karlp/hubbish/parts/1912251634_Ningbo-Kangnex-Elec-WJ2EDGRC-5-08-6P_C8435.pdf

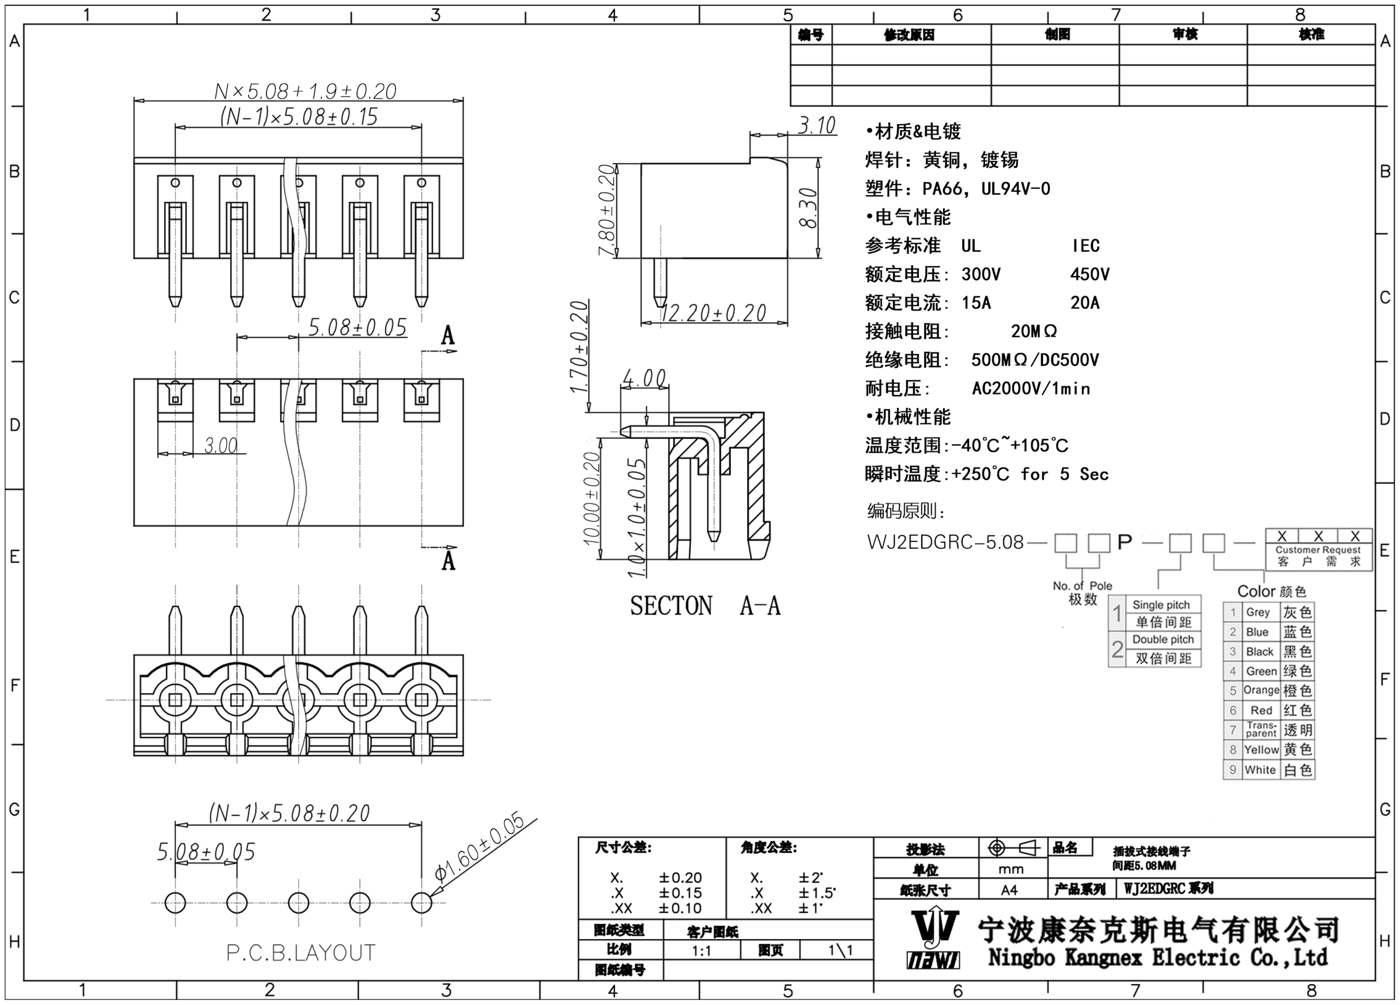
[picture p5: page 1]
