karlp/hubbish/parts/2002271812_XKB-Enterprise-U254-051T-4BH23-S2B_C319164.pdf

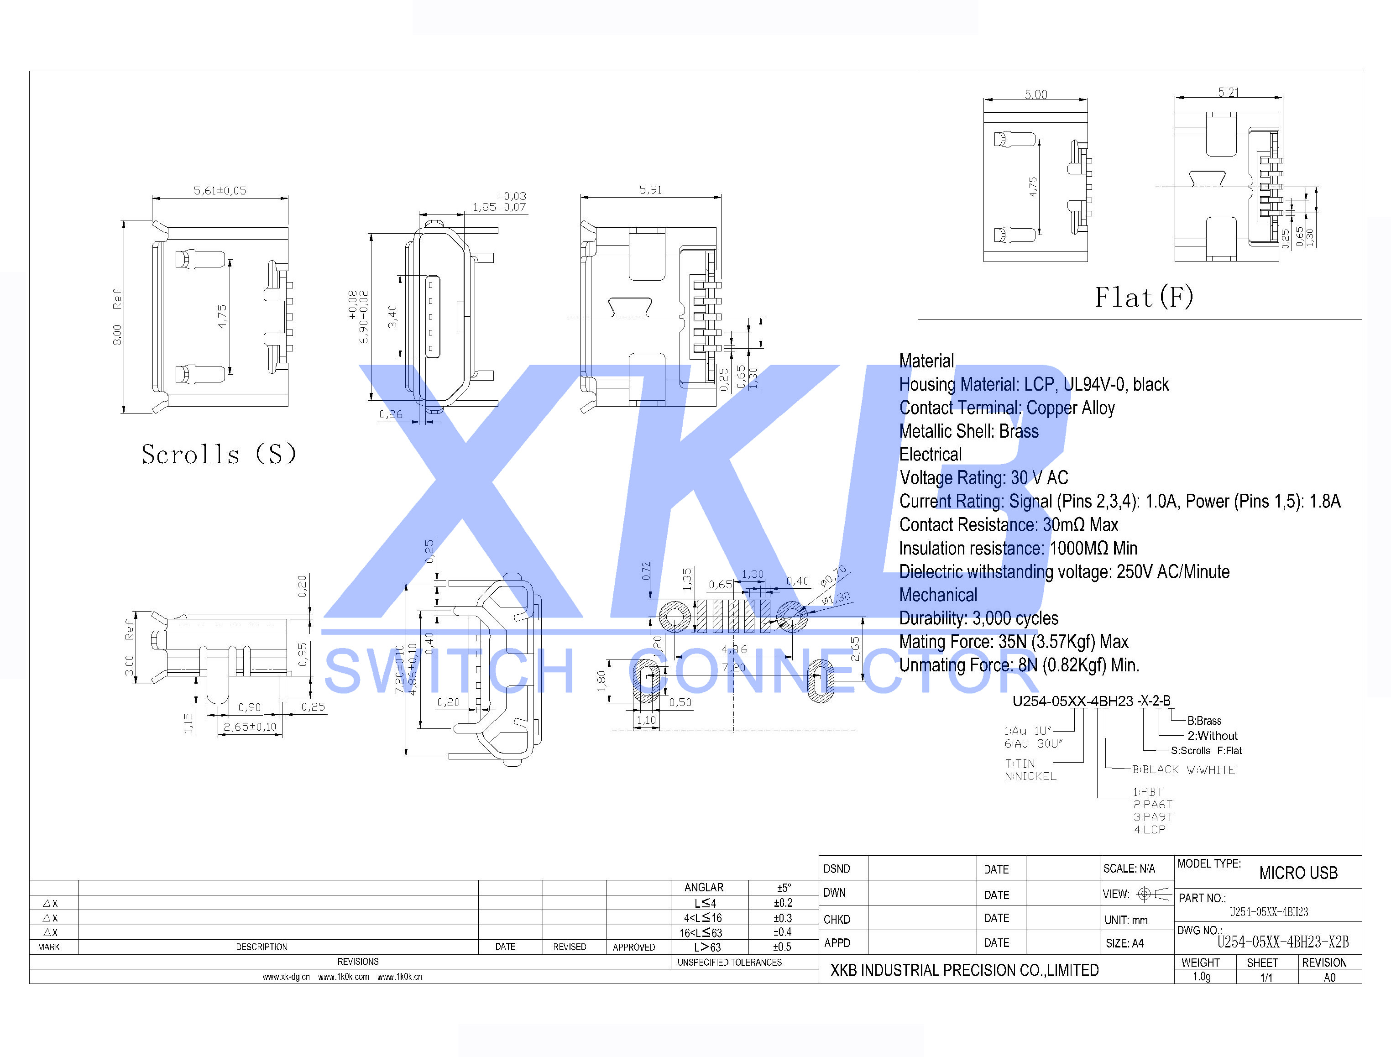
[picture p6: page 1]
