karlp/hubbish/parts/enclosures/ABS-35-deep-other.pdf

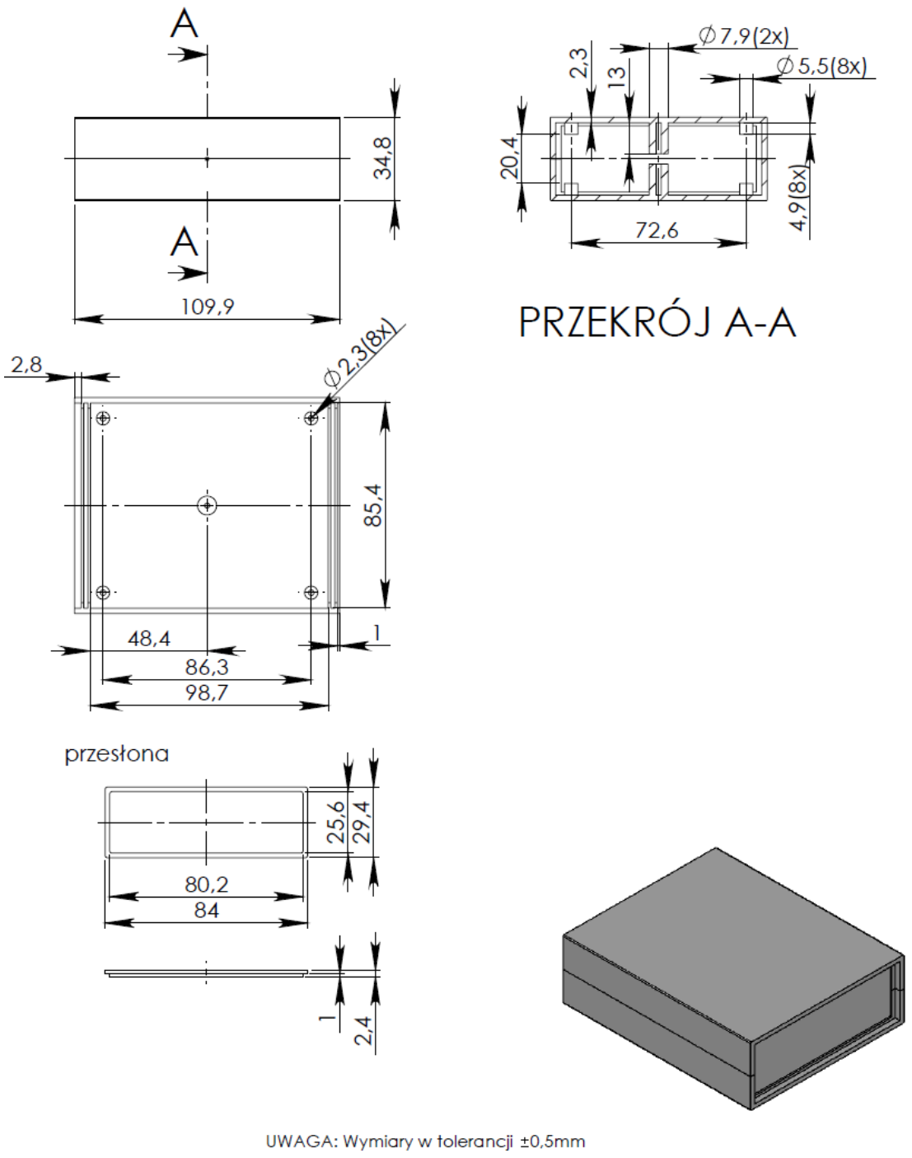
[picture p7: page 1]
