karlp/hubbish/parts/enclosures/abs-35-shallow.pdf

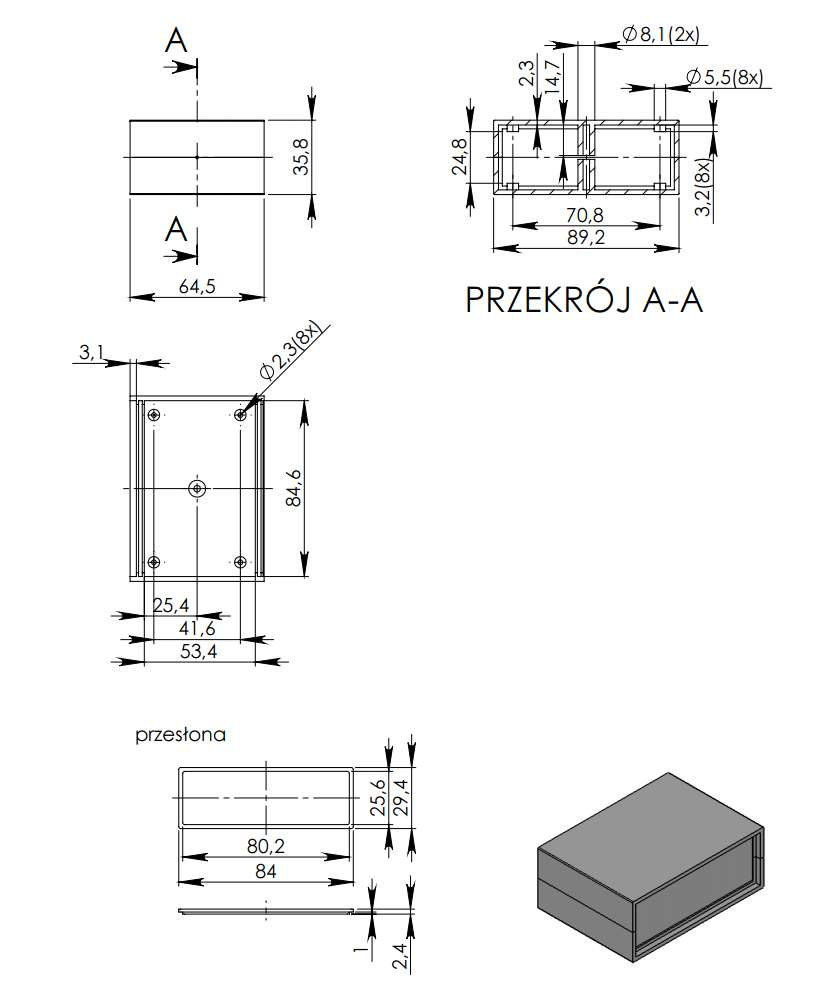
[picture p8: figure]
