karlp/hubbish/parts/enclosures/KM-35B-other-copy.pdf

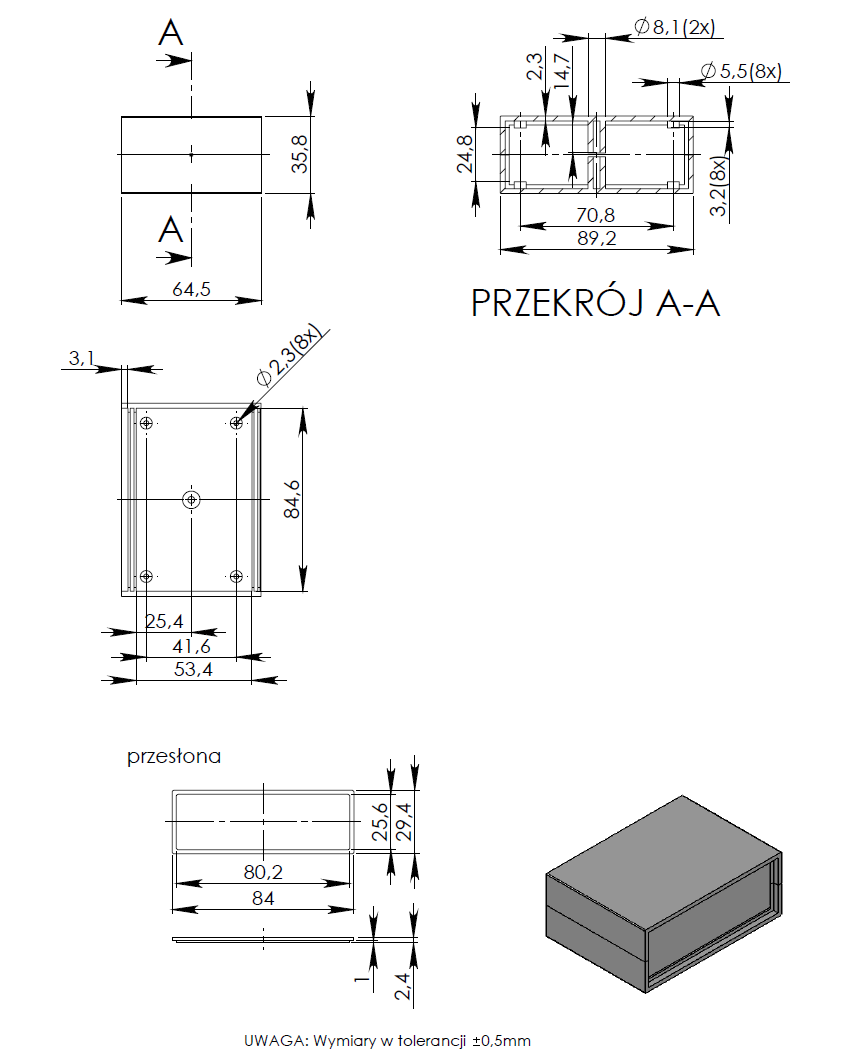
[picture p9: page 1]
