karlp/hubbish/r2020-03/usb-test-harness.pdf

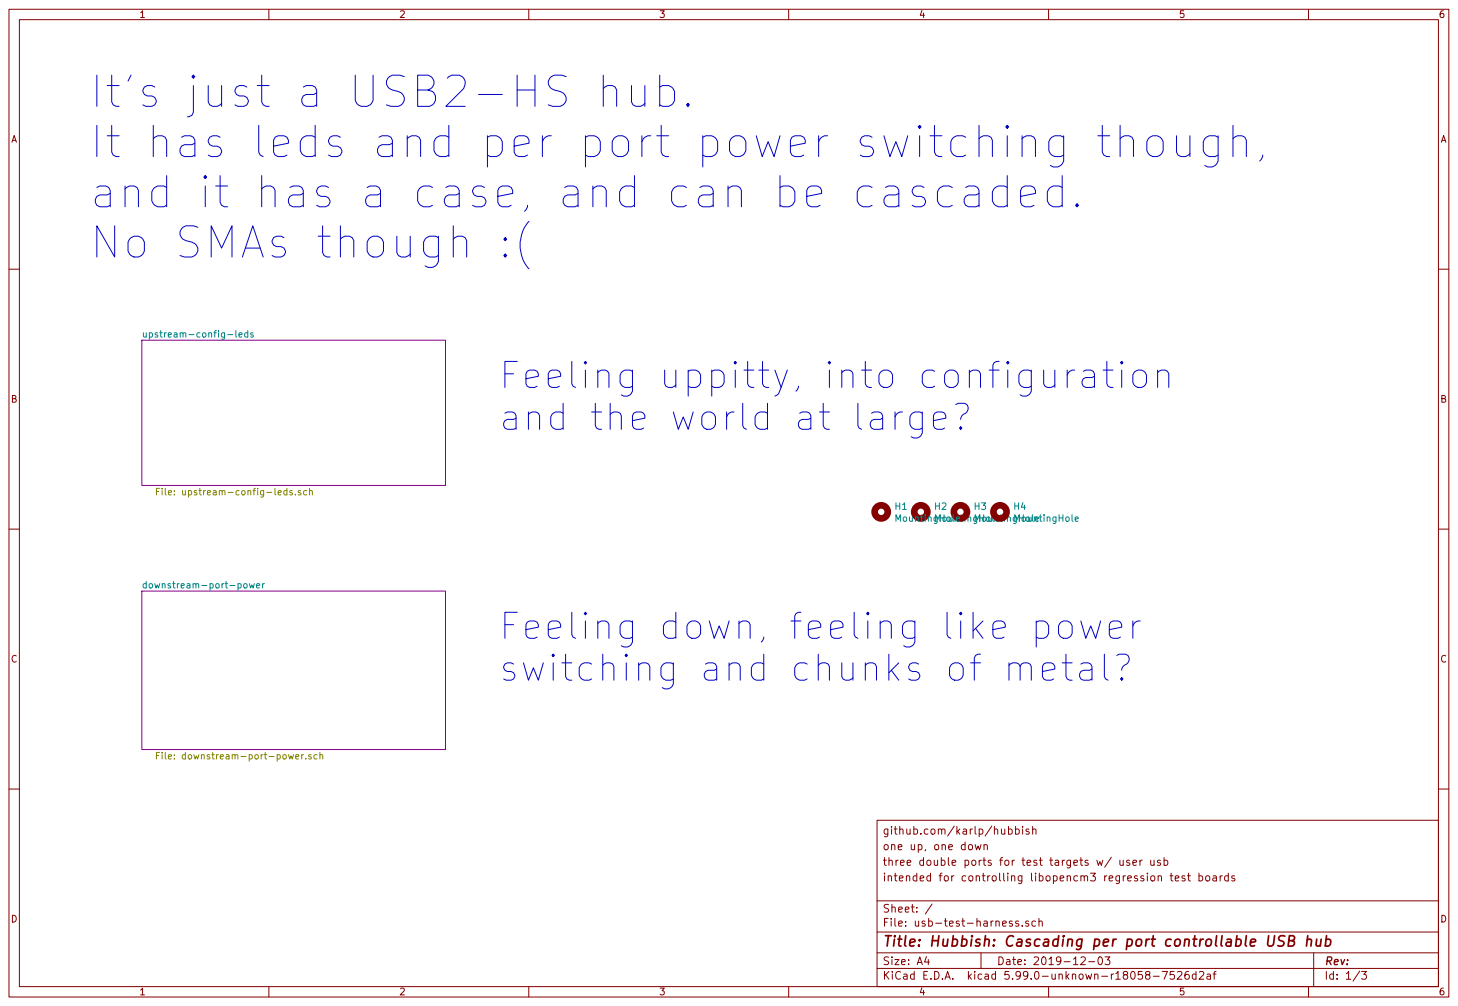
[picture p14: page 1]

It's just a USB2-HS hub.
It has leds and per port power switching though,
and it has a case, and can be cascaded.
No SMAs though :(

Feeling uppitty, into configuration
and the world at large?

Feeling down, feeling like power
switching and chunks of metal?

File: downstream-port-power.sch

github.com/karlp/hubbish
one up, one down
three double ports for test targets w/ user usb
intended for controlling libopencm3 regression test boards

File: usb-test-harness.sch Sheet: /
Id: 1/3 Title: Hubbish: Cascading per port controllable USB hub

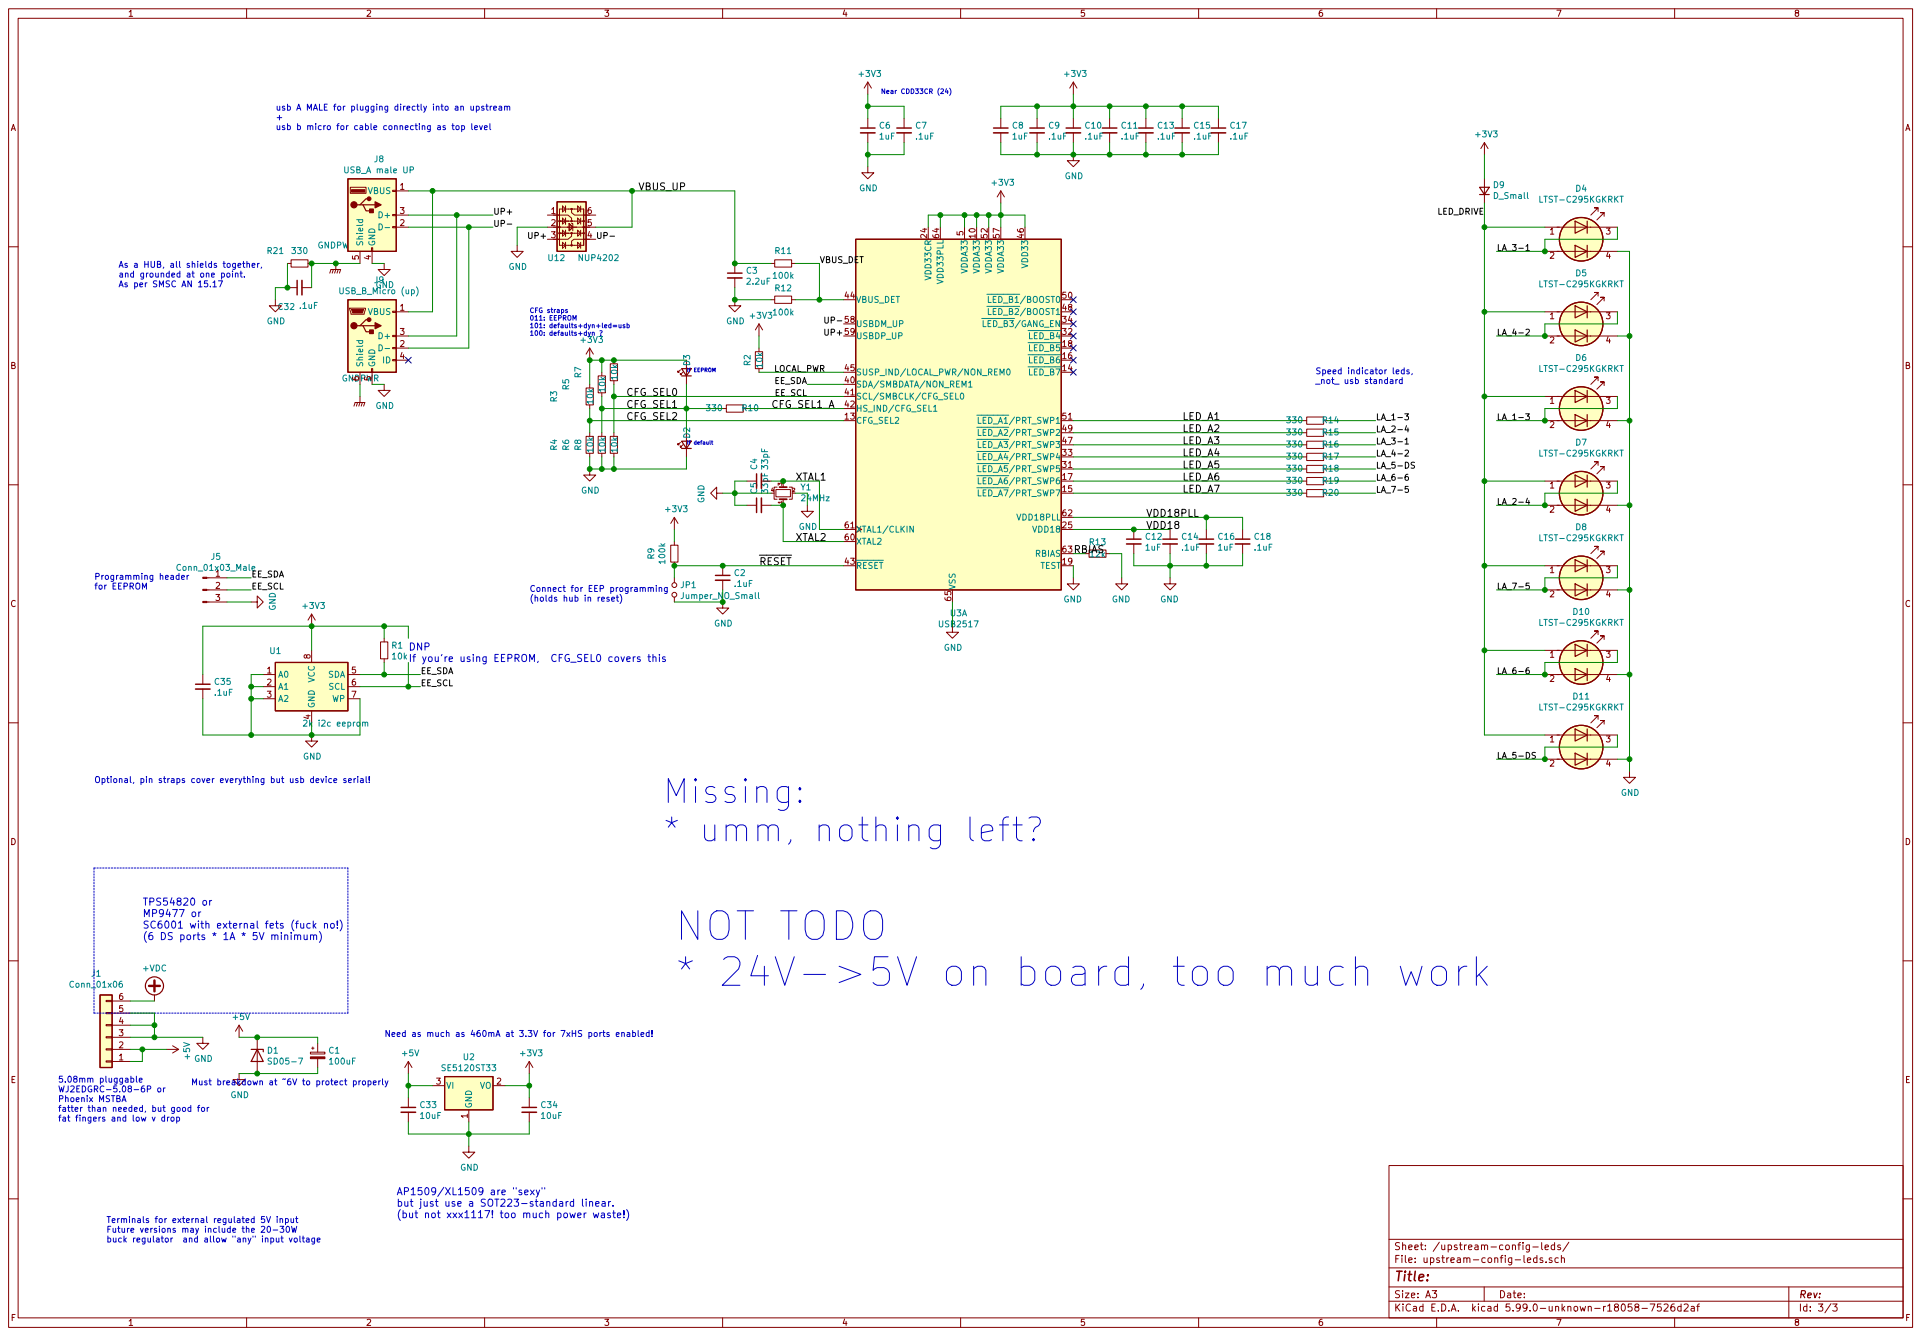
[picture p15: page 2]

usb A MALE for plugging directly into an upstream
usb b micro for cable connecting as top level

As a HUB, all shields together,
and grounded at one point.
As per SMSC AN 15.17

101: defaults+dyn+led=usb
100: defaults+dyn ?

Speed indicator leds, _not_ usb standard Must breakdown at 6V to protect properly

(holds hub in reset)

DNP
If you're using EEPROM, CFG_SEL0 covers this
EE_SCL EE_SDA

4 SDA 5 SCL 6 WP 7 VCC

Optional, pin straps cover everything but usb device serial!

buck regulator and allow "any" input voltage TPS54820 or MP9477 or SC6001 with external fets (fuck no!)

NOT TODO
* 24V->5V on board, too much work

Need as much as 460mA at 3.3V for 7xHS ports enabled!

5.08mm pluggable WJ2EDGRC-5.08-6P or Phoenix MSTBA

fatter than needed, but good for
fat fingers and low v drop

AP1509/XL1509 are "sexy"
but just use a SOT223-standard linear.
(but not xxx1117! too much power waste!)

Terminals for external regulated 5V input
Future versions may include the 20-30W

Sheet: /upstream-config-leds/
File: upstream-config-leds.sch
Id: 3/3 Title:

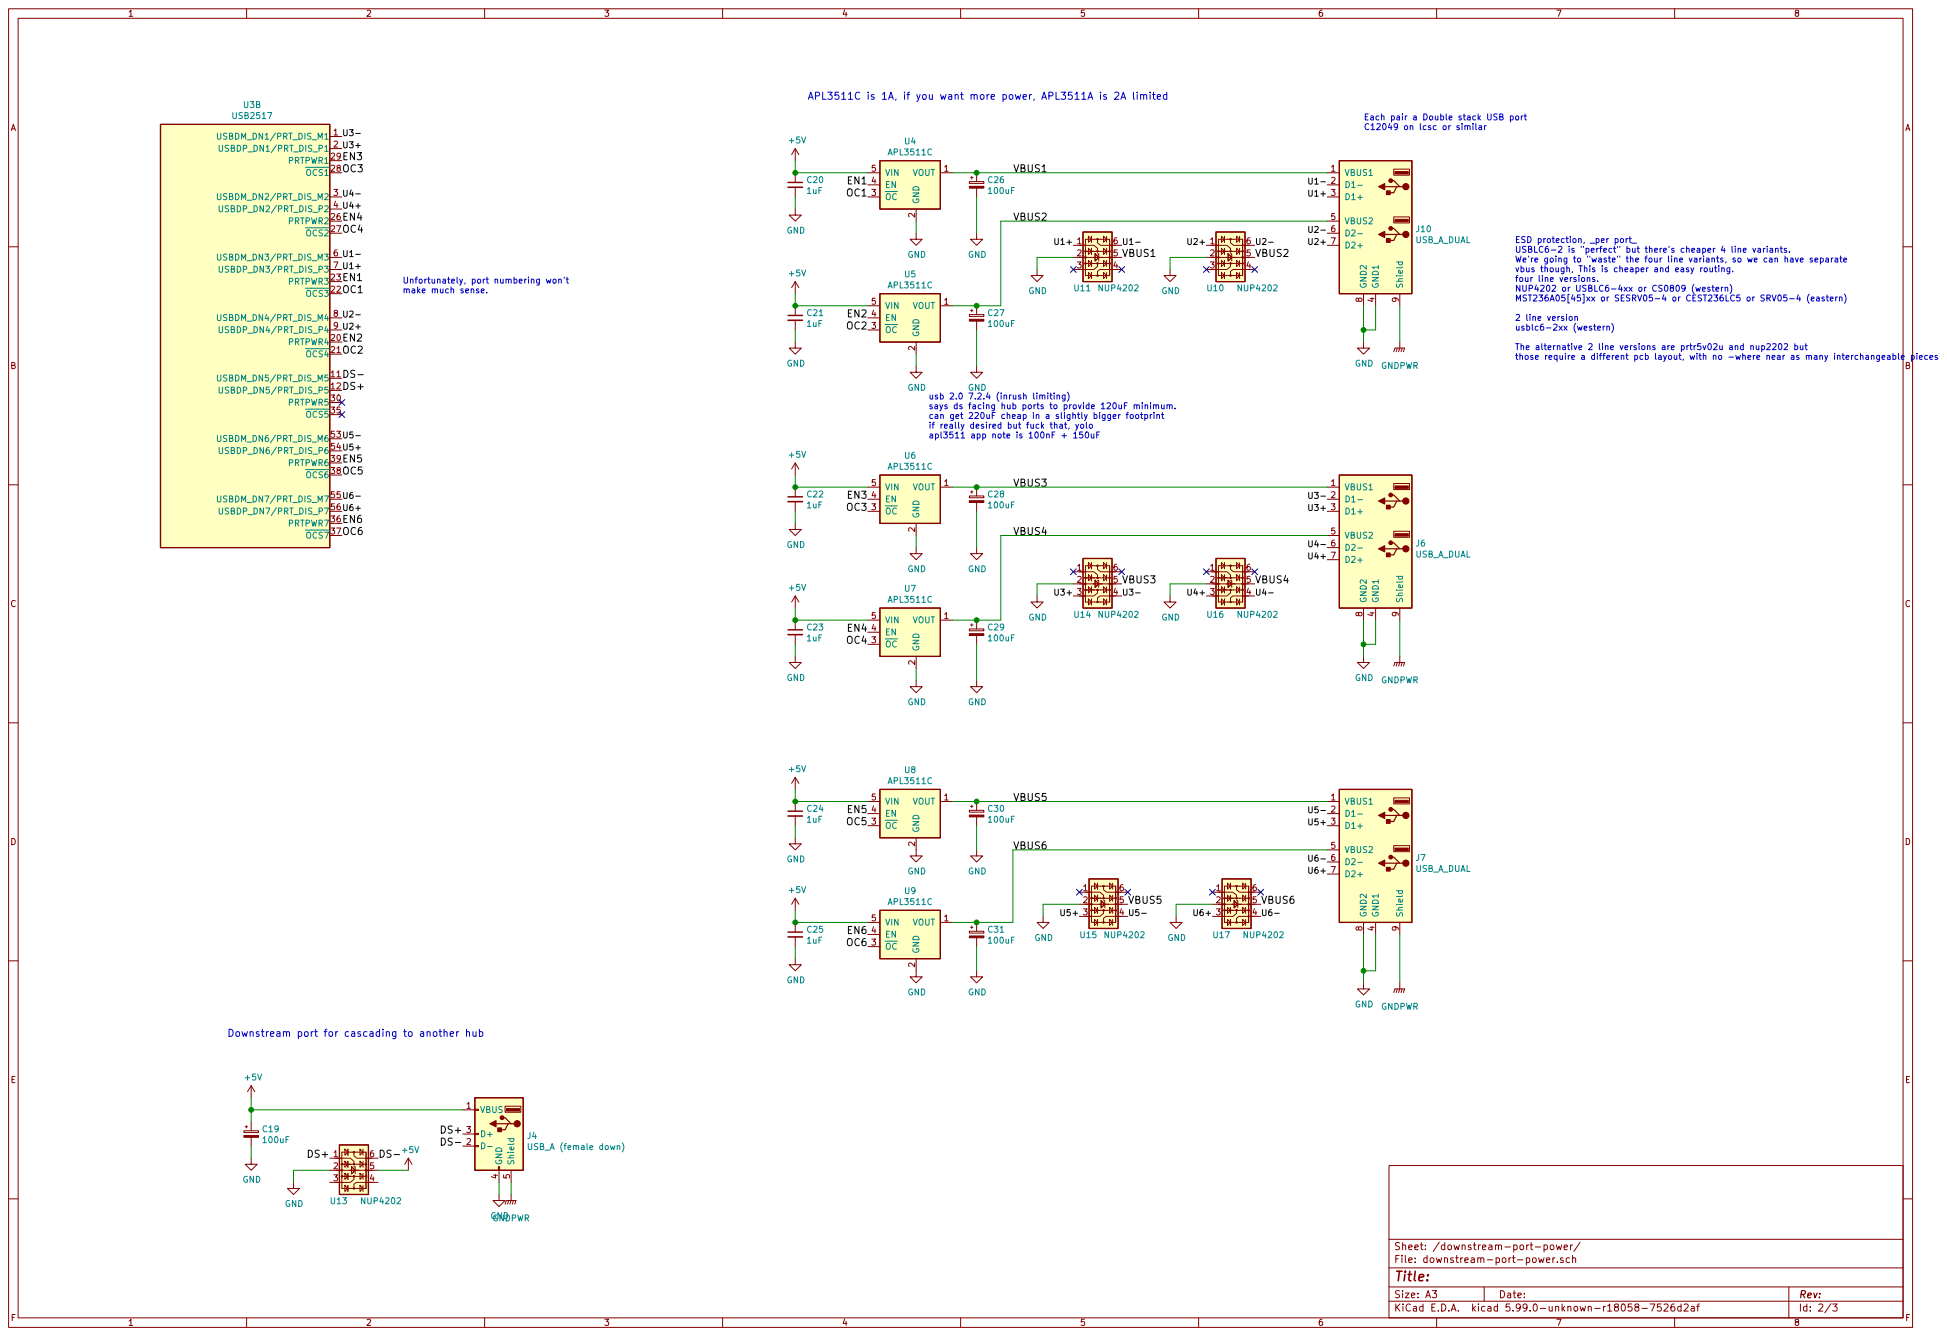
[picture p16: page 3]

2 OC 3 EN 4 VIN 5 U4 APL3511C GND

ESD protection, _per port_
USBLC6-2 is "perfect" but there's cheaper 4 line variants.
We're going to "waste" the four line variants, so we can have separate
vbus though, This is cheaper and easy routing.
four line versions. NUP4202 or USBLC6-4xx or CS0809 (western)

MST236A05[45]xx or SESRV05-4 or CEST236LC5 or SRV05-4 (eastern) 2 line version

The alternative 2 line versions are prtr5v02u and nup2202 but
those require a different pcb layout, with no -where near as many interchangeable pieces

says ds facing hub ports to provide 120uF minimum.
can get 220uF cheap in a slightly bigger footprint
if really desired but fuck that, yolo
apl3511 app note is 100nF + 150uF

2 OC 3 EN 4 VIN 5 U9 APL3511C GND

Downstream port for cascading to another hub

Sheet: /downstream-port-power/ C19

J4USB_A (female down) GND GNDPWR

File: downstream-port-power.sch
Id: 2/3 Title:
