karlp/hubbish/parts/enclosures/bud-hb-cu18428.pdf

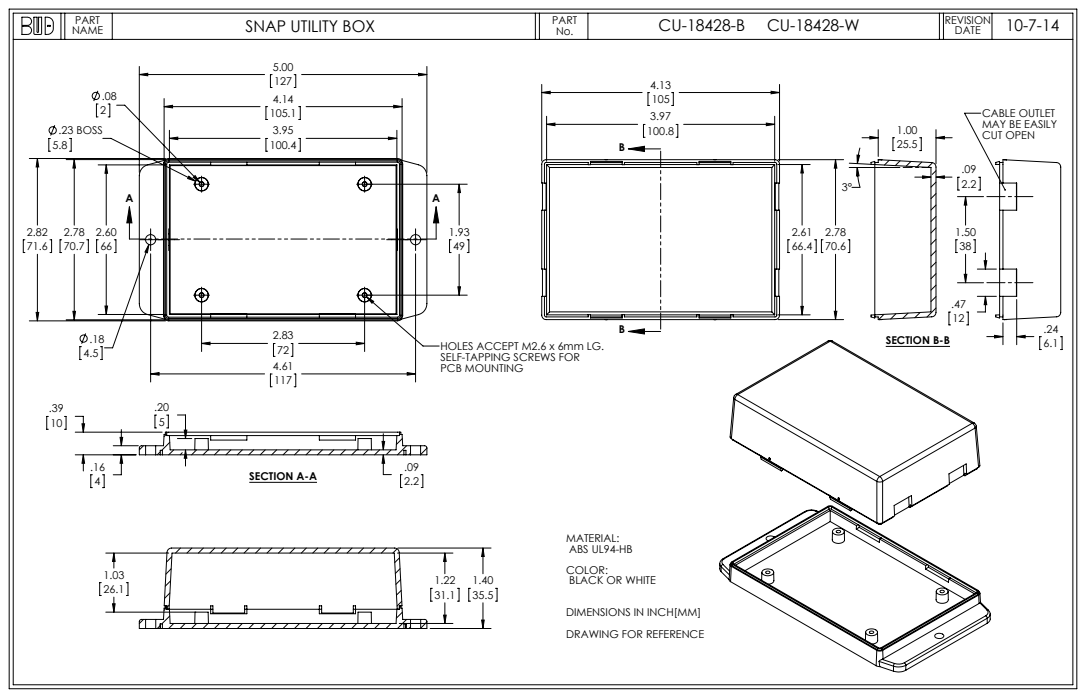
[picture p18: page 1]
2.2 SECTION A-A; SECTION B-B; SNAP UTILITY BOX; 10-7-14 PART

CABLE OUTLET
MAY BE EASILY
CUT OPEN

HOLES ACCEPT M2.6 x 6mm LG.
SELF-TAPPING SCREWS FOR
PCB MOUNTING

MATERIAL:
ABS UL94-HB
COLOR:
BLACK OR WHITE

DIMENSIONS IN INCH[MM]
DRAWING FOR REFERENCE
