karlp/hubbish/parts/enclosures/KM-536B.pdf

A
(skala 1:1) | 90

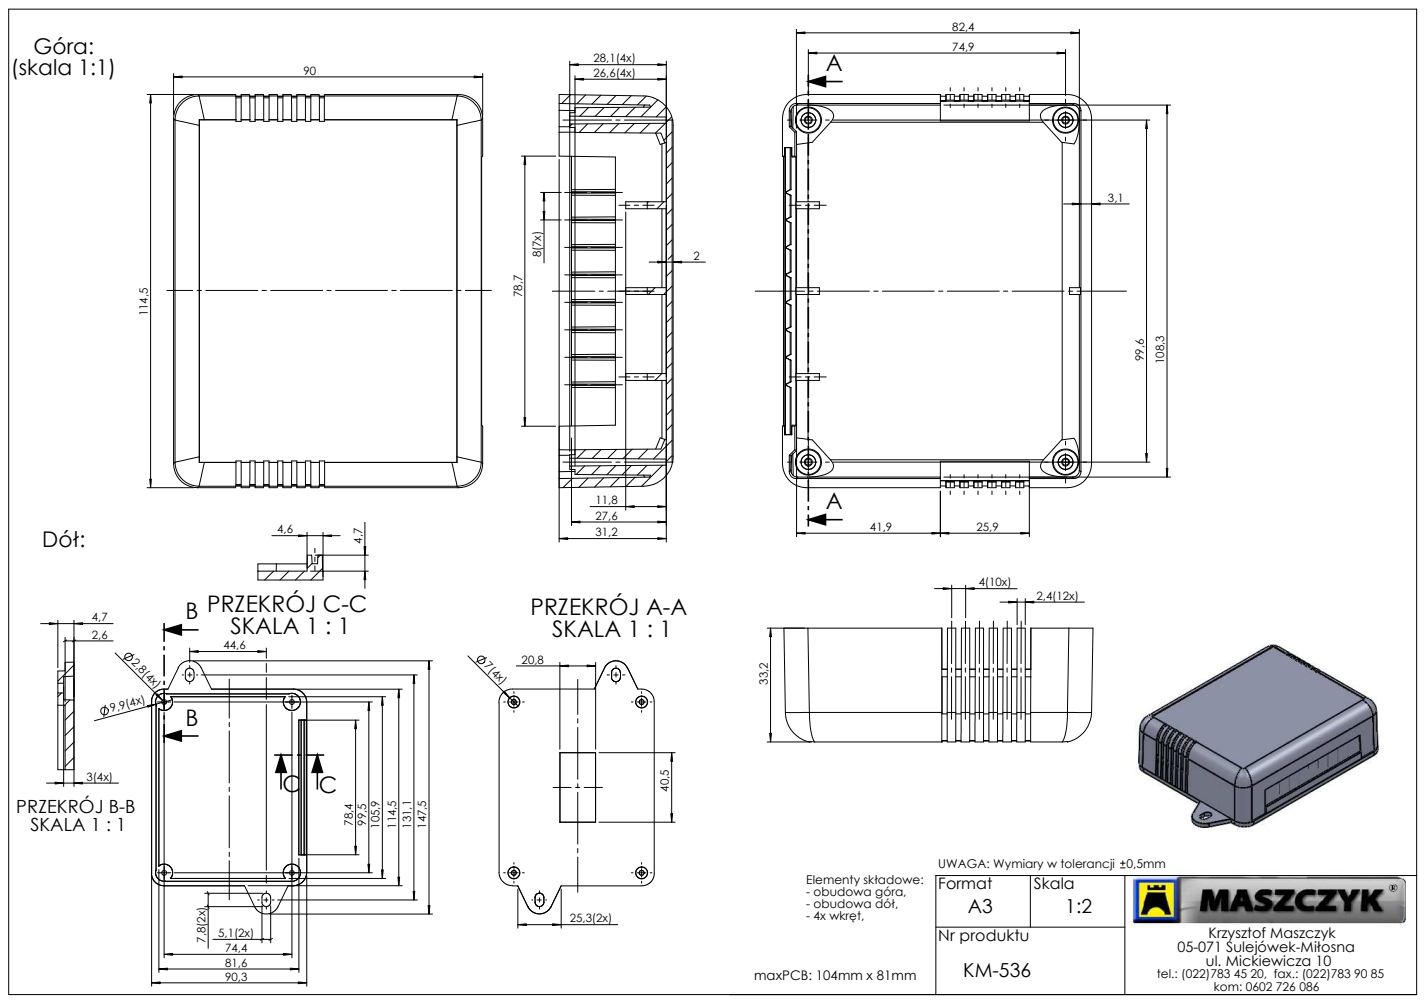
[picture p19: page 1]
PRZEKRÓJ A-A SKALA 1 : 1; PRZEKRÓJ C-C SKALA 1 : 1; PRZEKRÓJ B-B SKALA 1 : 1; maxPCB: 104mm x 81mm; Góra:; Dół:; tel.: (022)783 45 20, fax.: (022)783 90 85 kom: 0602 726 086; - 4x wkręt,; - obudowa góra, - obudowa dół,; Nr produktu; Format; Skala; Krzysztof Maszczyk; Elementy składowe:; ul. Mickiewicza 10; 05-071 Sulejówek-Miłosna

UWAGA: Wymiary w tolerancji
