karlp/hubbish/r2022-10/hubbish-rev3-2022-10.pdf

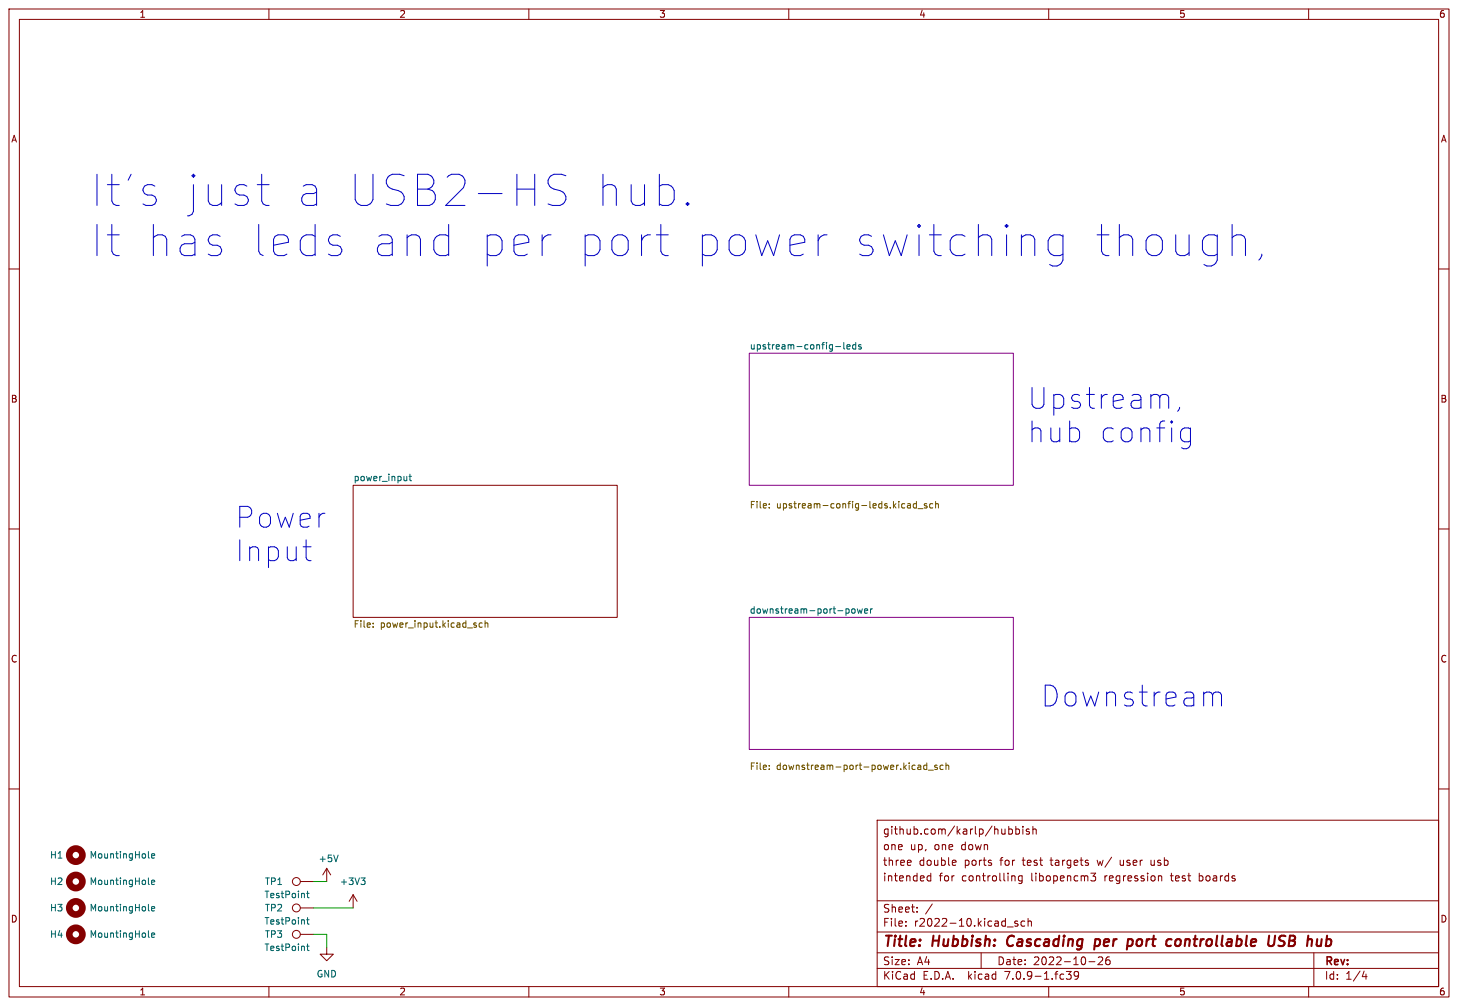
[picture p20: page 1]

upstream-config-leds File: upstream-config-leds.kicad_sch

downstream-port-power File: downstream-port-power.kicad_sch

github.com/karlp/hubbish
one up, one down

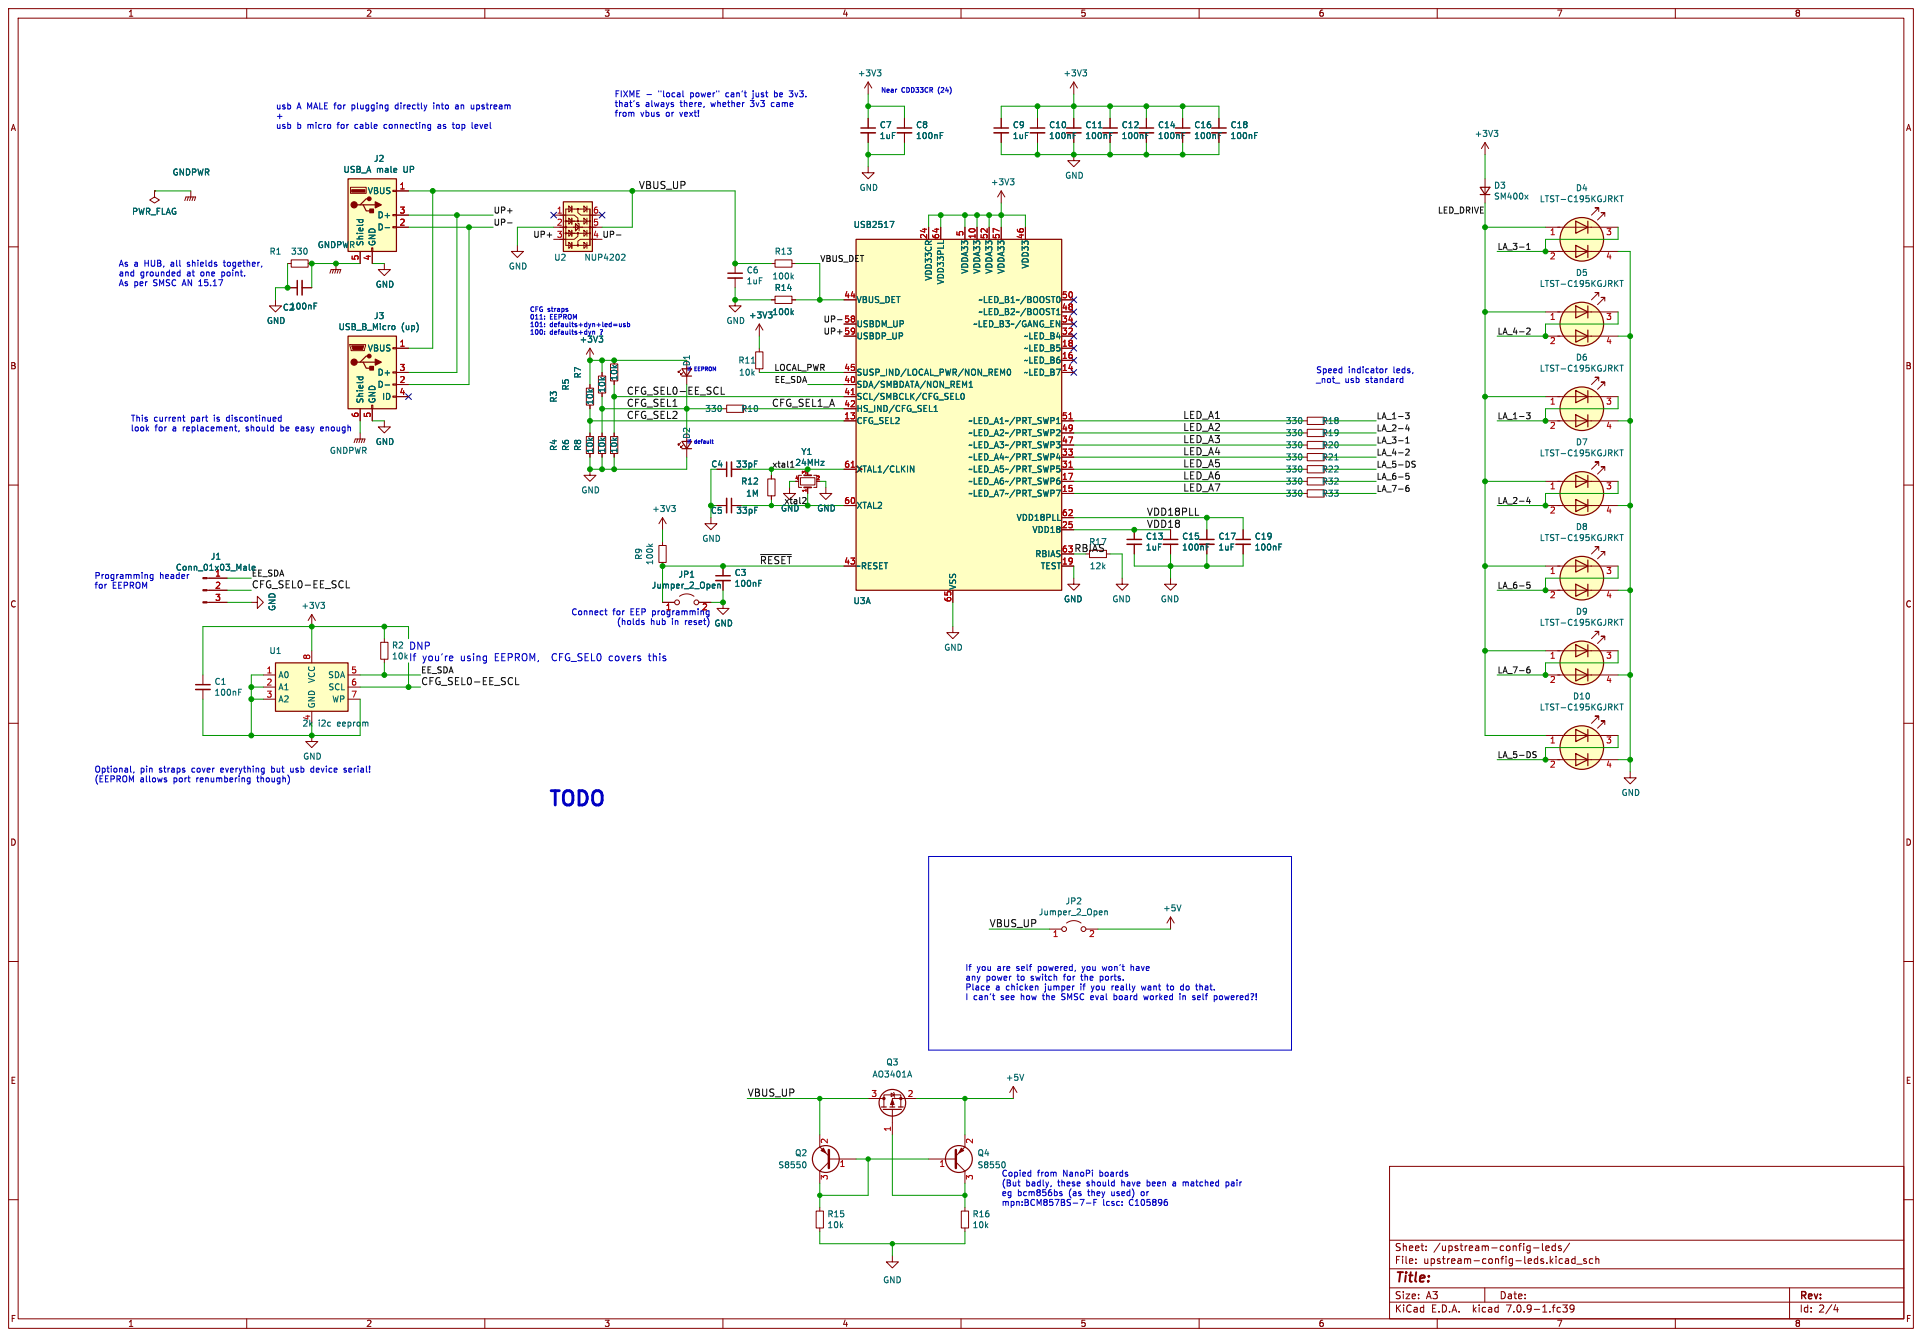
[picture p21: page 2]

that's always there, whether 3v3 came
from vbus or vext!

5 ~LED_B1~/BOOST0 50 ~LED_A1~/PRT_SWP1 51 VDDA33 52 VDDA33 57 USBDM_UP 58 USBDP_UP 59 XTAL2 60 XTAL1/CLKIN 61 VDD18PLL 62 RBIAS 63 VDD33PLL 64 VSS U3A 65 USB2517 GND GND +3V3

J3 USB_B_Micro (up) GND
If you're using EEPROM, CFG_SEL0 covers this GND

If default CFG straps 011: EEPROM

101: defaults+dyn+led=usb

(holds hub in reset)

4 SDA 5 SCL 6 WP 7 VCC

If you are self powered, you won't have
any power to switch for the ports. Place a chicken jumper if you really want to do that.

I can't see how the SMSC eval board worked in self powered?!

Copied from NanoPi boards

Id: 2/4 Title: File: upstream-config-leds.kicad_sch Sheet: /upstream-config-leds/

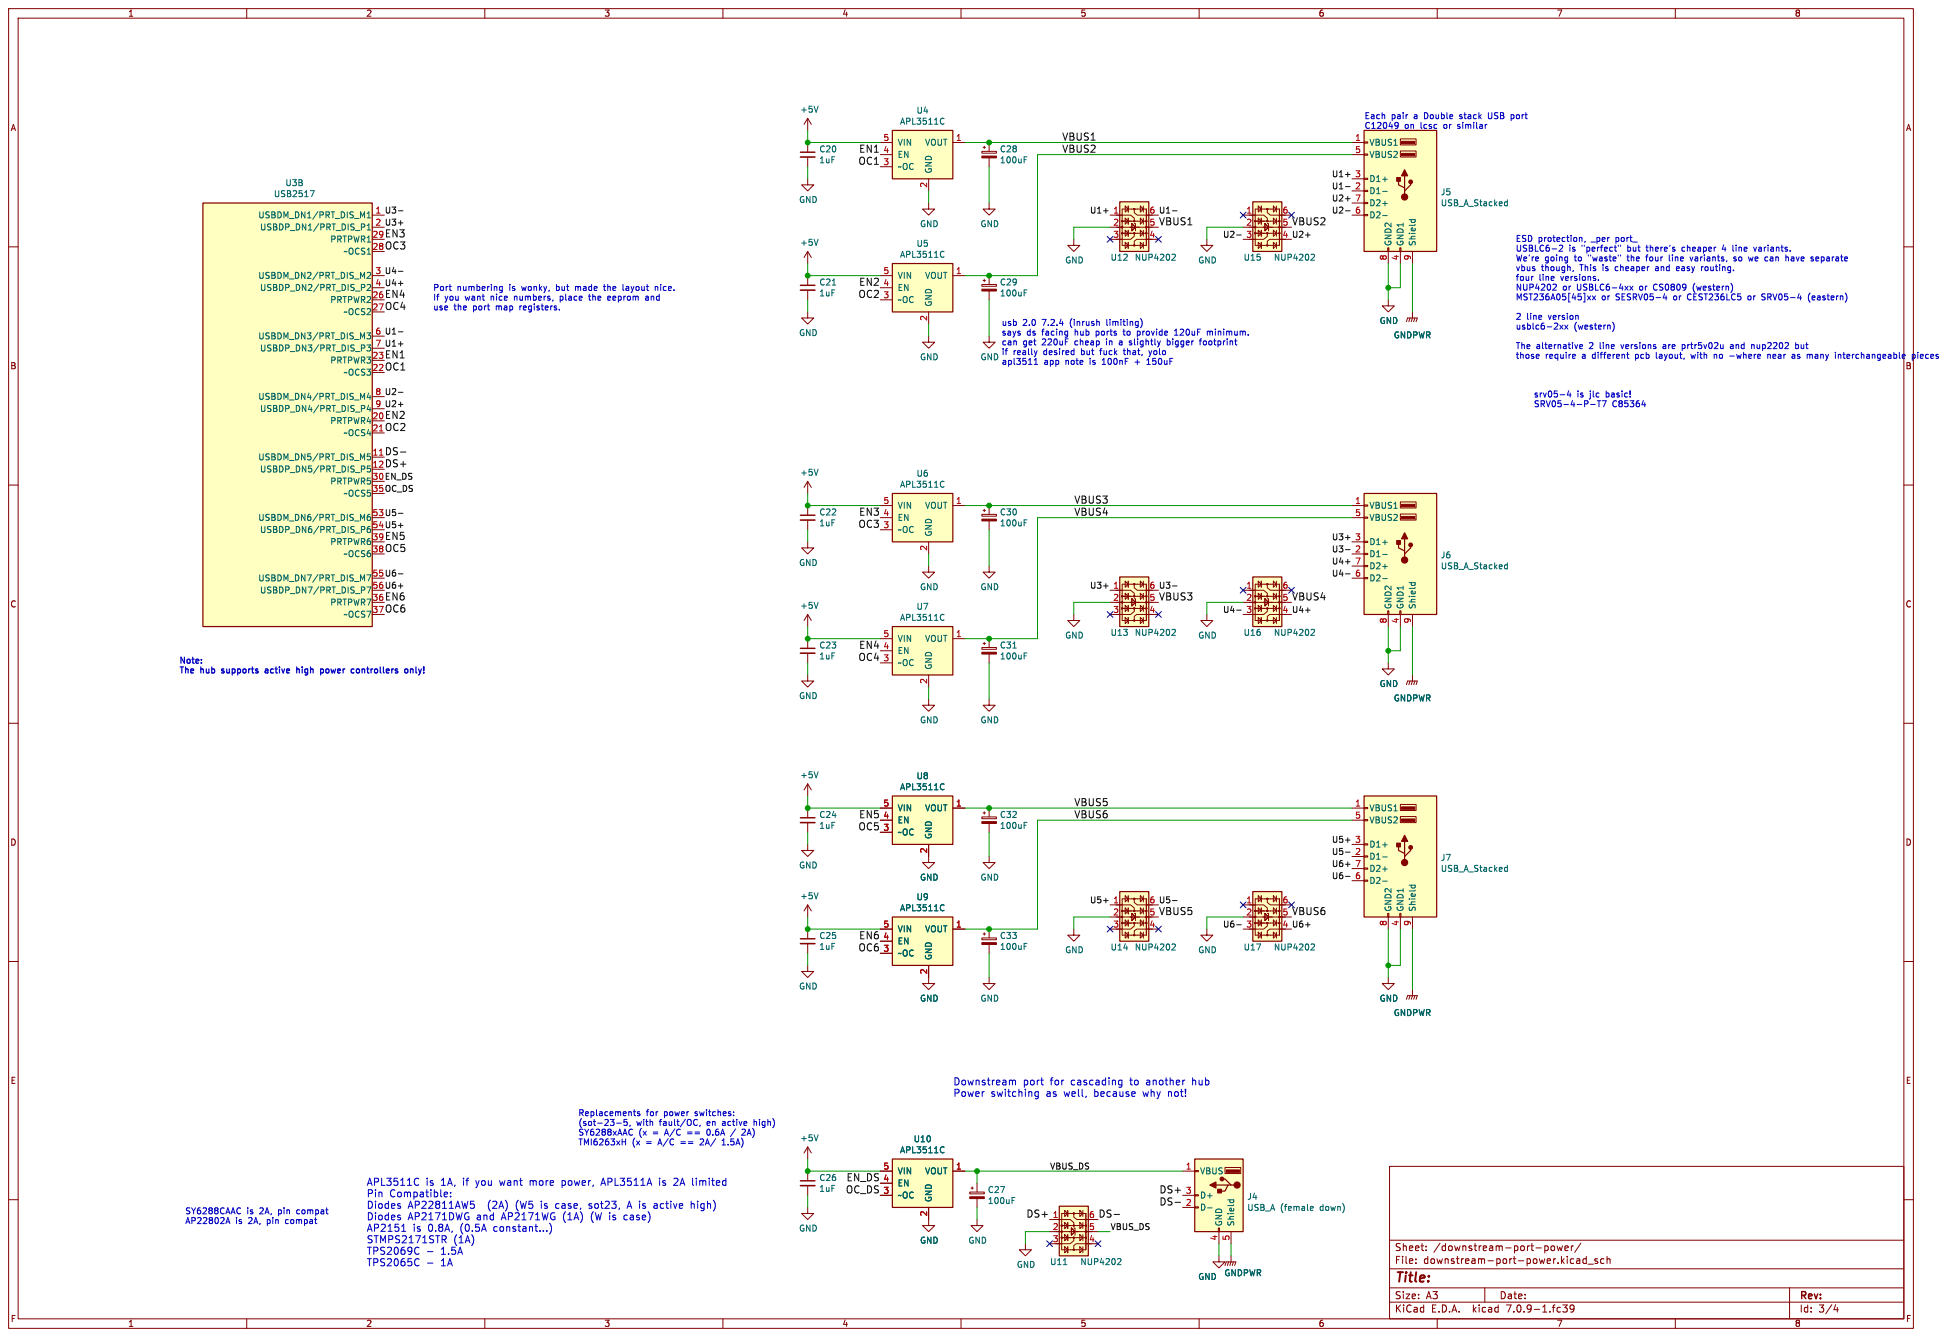
[picture p22: page 3]

vbus though, This is cheaper and easy routing.

If you want nice numbers, place the eeprom and
use the port map registers.

GNDPWR GND GNDGNDPWR GND

if really desired but fuck that, yolo

2 ~OC 3 EN 4 VIN 5 U6 APL3511C GND GND

2 ~OC 3 EN 4 VIN 5 U7 APL3511C GND

2 ~OC 3 EN 4 VIN 5 U8 APL3511C GND GND

2 ~OC 3 EN 4 VIN 5 GNDGNDPWR

2 ~OC 3 EN 4 VIN 5 GND

Id: 3/4 Title: File: downstream-port-power.kicad_sch Sheet: /downstream-port-power/ C33

2 ~OC 3 EN 4 VIN 5 U10 APL3511C GND

2 ~OC 3 EN 4 VIN 5 GND GND GNDPWR

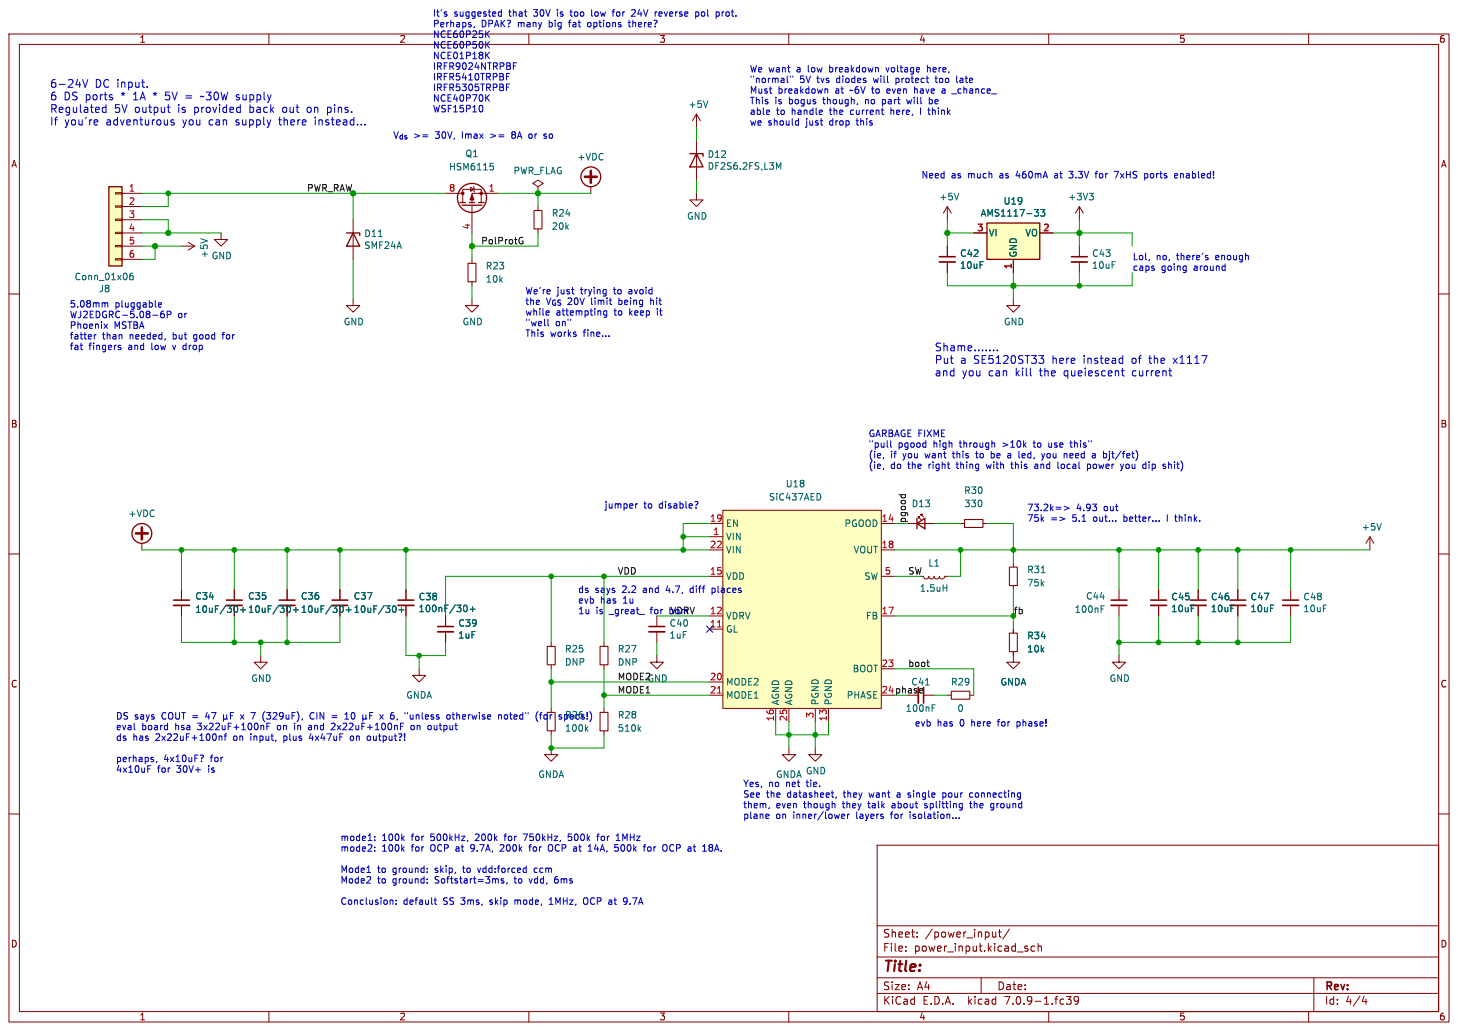
[picture p23: page 4]

Regulated 5V output is provided back out on pins.

evb has 0 here for phase! We're just trying to avoid

fatter than needed, but good for
fat fingers and low v drop

(ie, do the right thing with this and local power you dip shit) Shame....... Put a SE5120ST33 here instead of the x1117

"pull pgood high through >10k to use this"
(ie, if you want this to be a led, you need a bjt/fet)

ds says 2.2 and 4.7, diff places evb has 1u

perhaps, 4x10uF? for 4x10uF for 30V+ is

Id: 4/4 Title: File: power_input.kicad_sch Sheet: /power_input/
