karlp/hubbish/r2021-02/hubbish-rev2.pdf

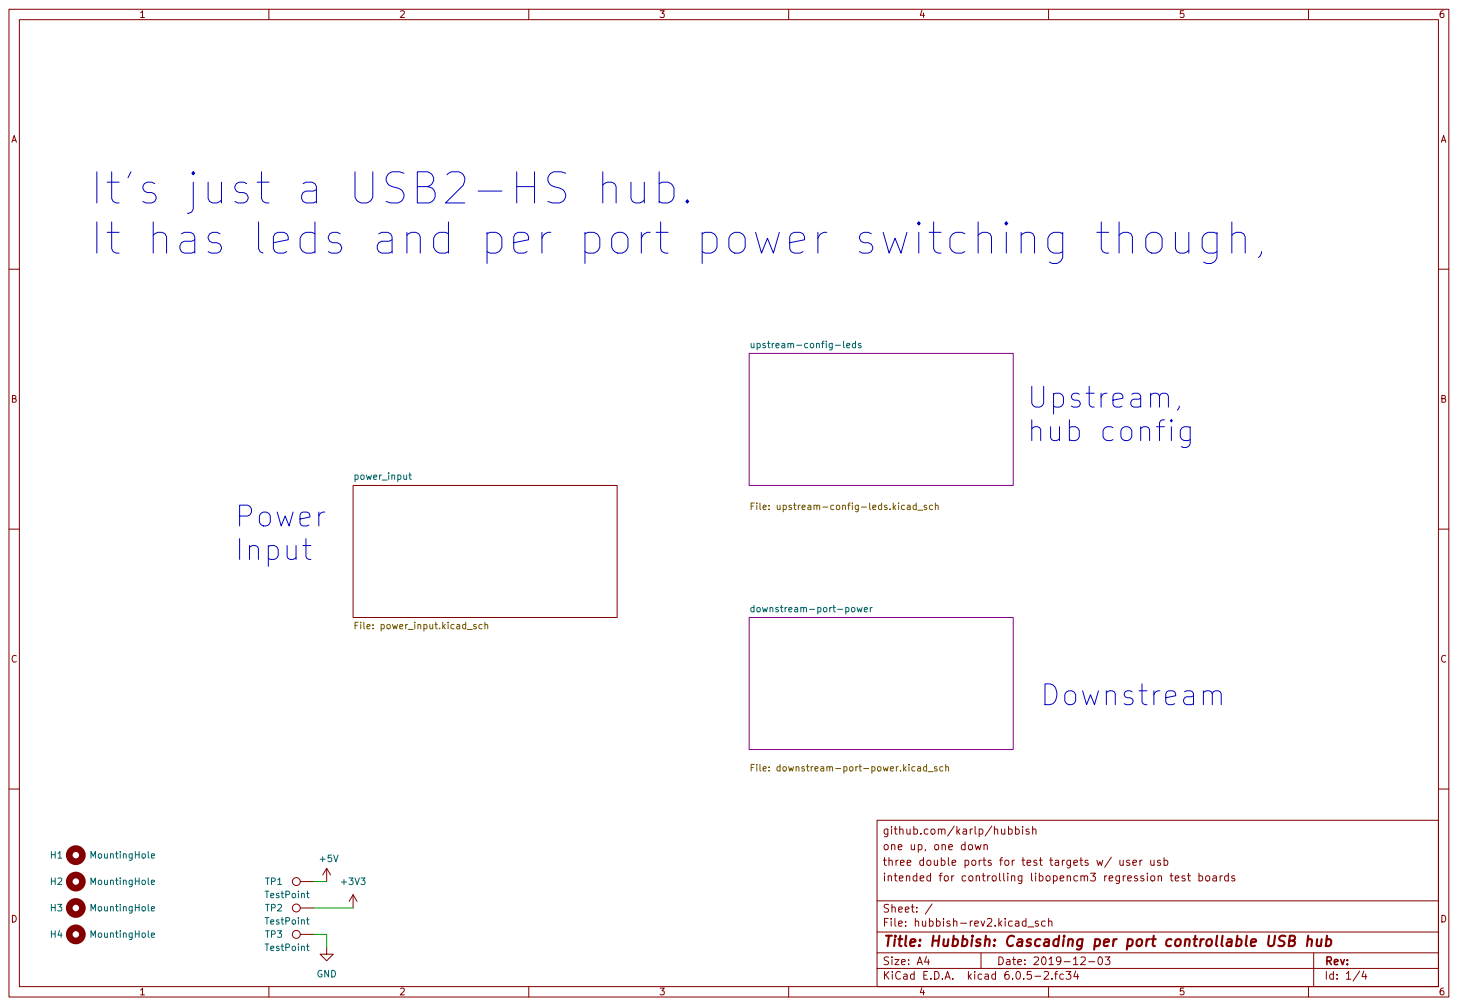
[picture p24: page 1]

It's just a USB2-HS hub.
It has leds and per port power switching though,

File: upstream-config-leds.kicad_sch

File: downstream-port-power.kicad_sch

github.com/karlp/hubbish
one up, one down
three double ports for test targets w/ user usb
intended for controlling libopencm3 regression test boards

File: hubbish-rev2.kicad_sch Sheet: /
Id: 1/4 Title: Hubbish: Cascading per port controllable USB hub

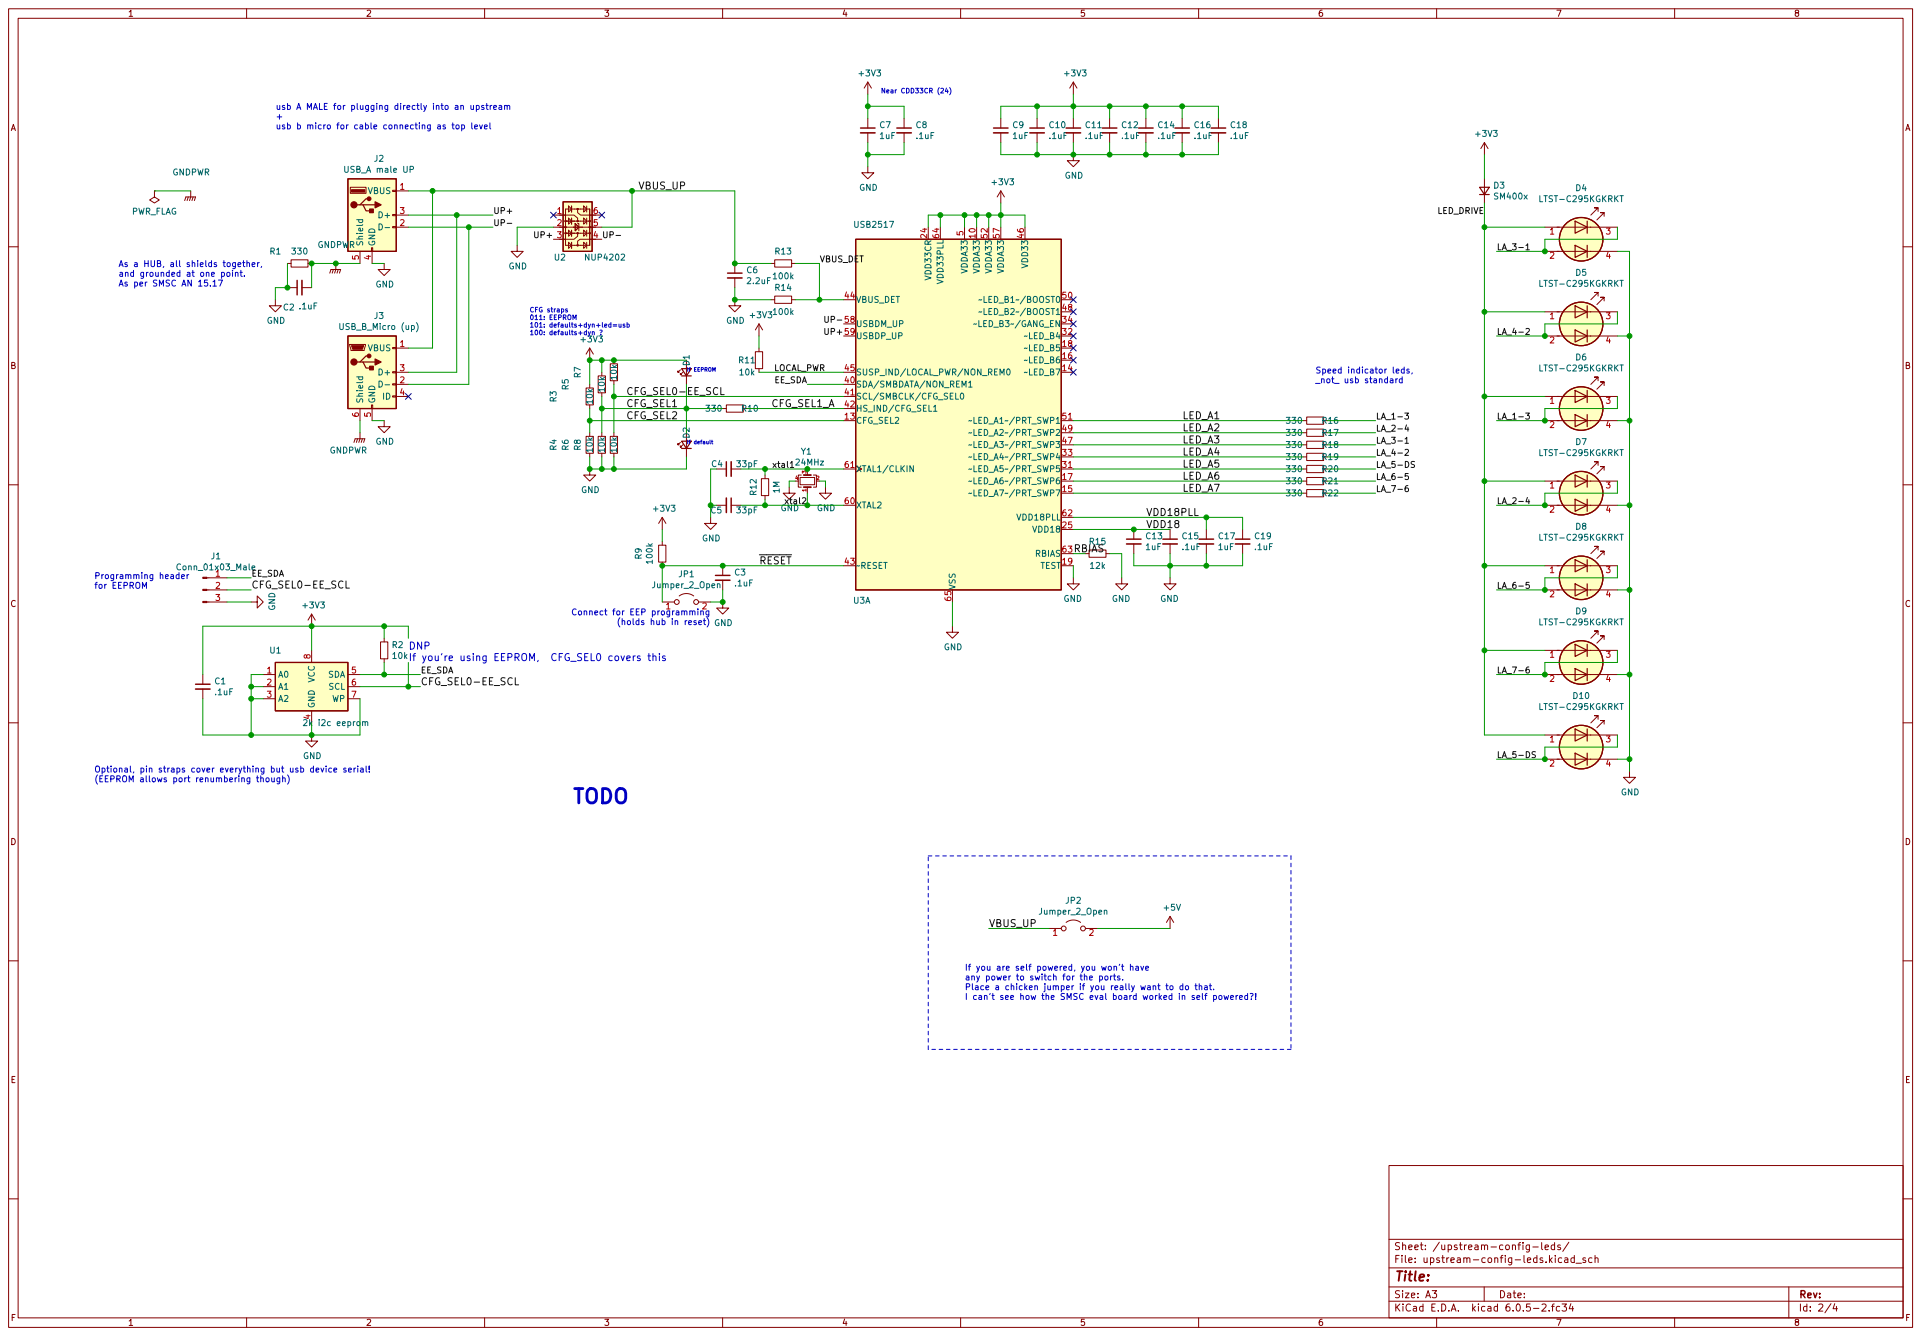
[picture p25: page 2]

usb A MALE for plugging directly into an upstream
usb b micro for cable connecting as top level

5 ~LED_B1~/BOOST050 ~LED_A1~/PRT_SWP151 VDDA33 52 VDDA33 57 USBDM_UP 58 USBDP_UP 59XTAL2 60XTAL1/CLKIN 61 VDD18PLL 62 RBIAS 63 VDD33PLL 64 VSS U3A 65 USB2517 GND

100: defaults+dyn ? As a HUB, all shields together,
and grounded at one point.
As per SMSC AN 15.17

101: defaults+dyn+led=usb

If EEPROM Connect for EEP programming

(holds hub in reset)

If you're using EEPROM, CFG_SEL0 covers this

4 SDA 5 SCL 6 WP 7 VCC

Optional, pin straps cover everything but usb device serial!

If you are self powered, you won't have
any power to switch for the ports.
Place a chicken jumper if you really want to do that.
I can't see how the SMSC eval board worked in self powered?!

Sheet: /upstream-config-leds/
File: upstream-config-leds.kicad_sch
Id: 2/4 Title:

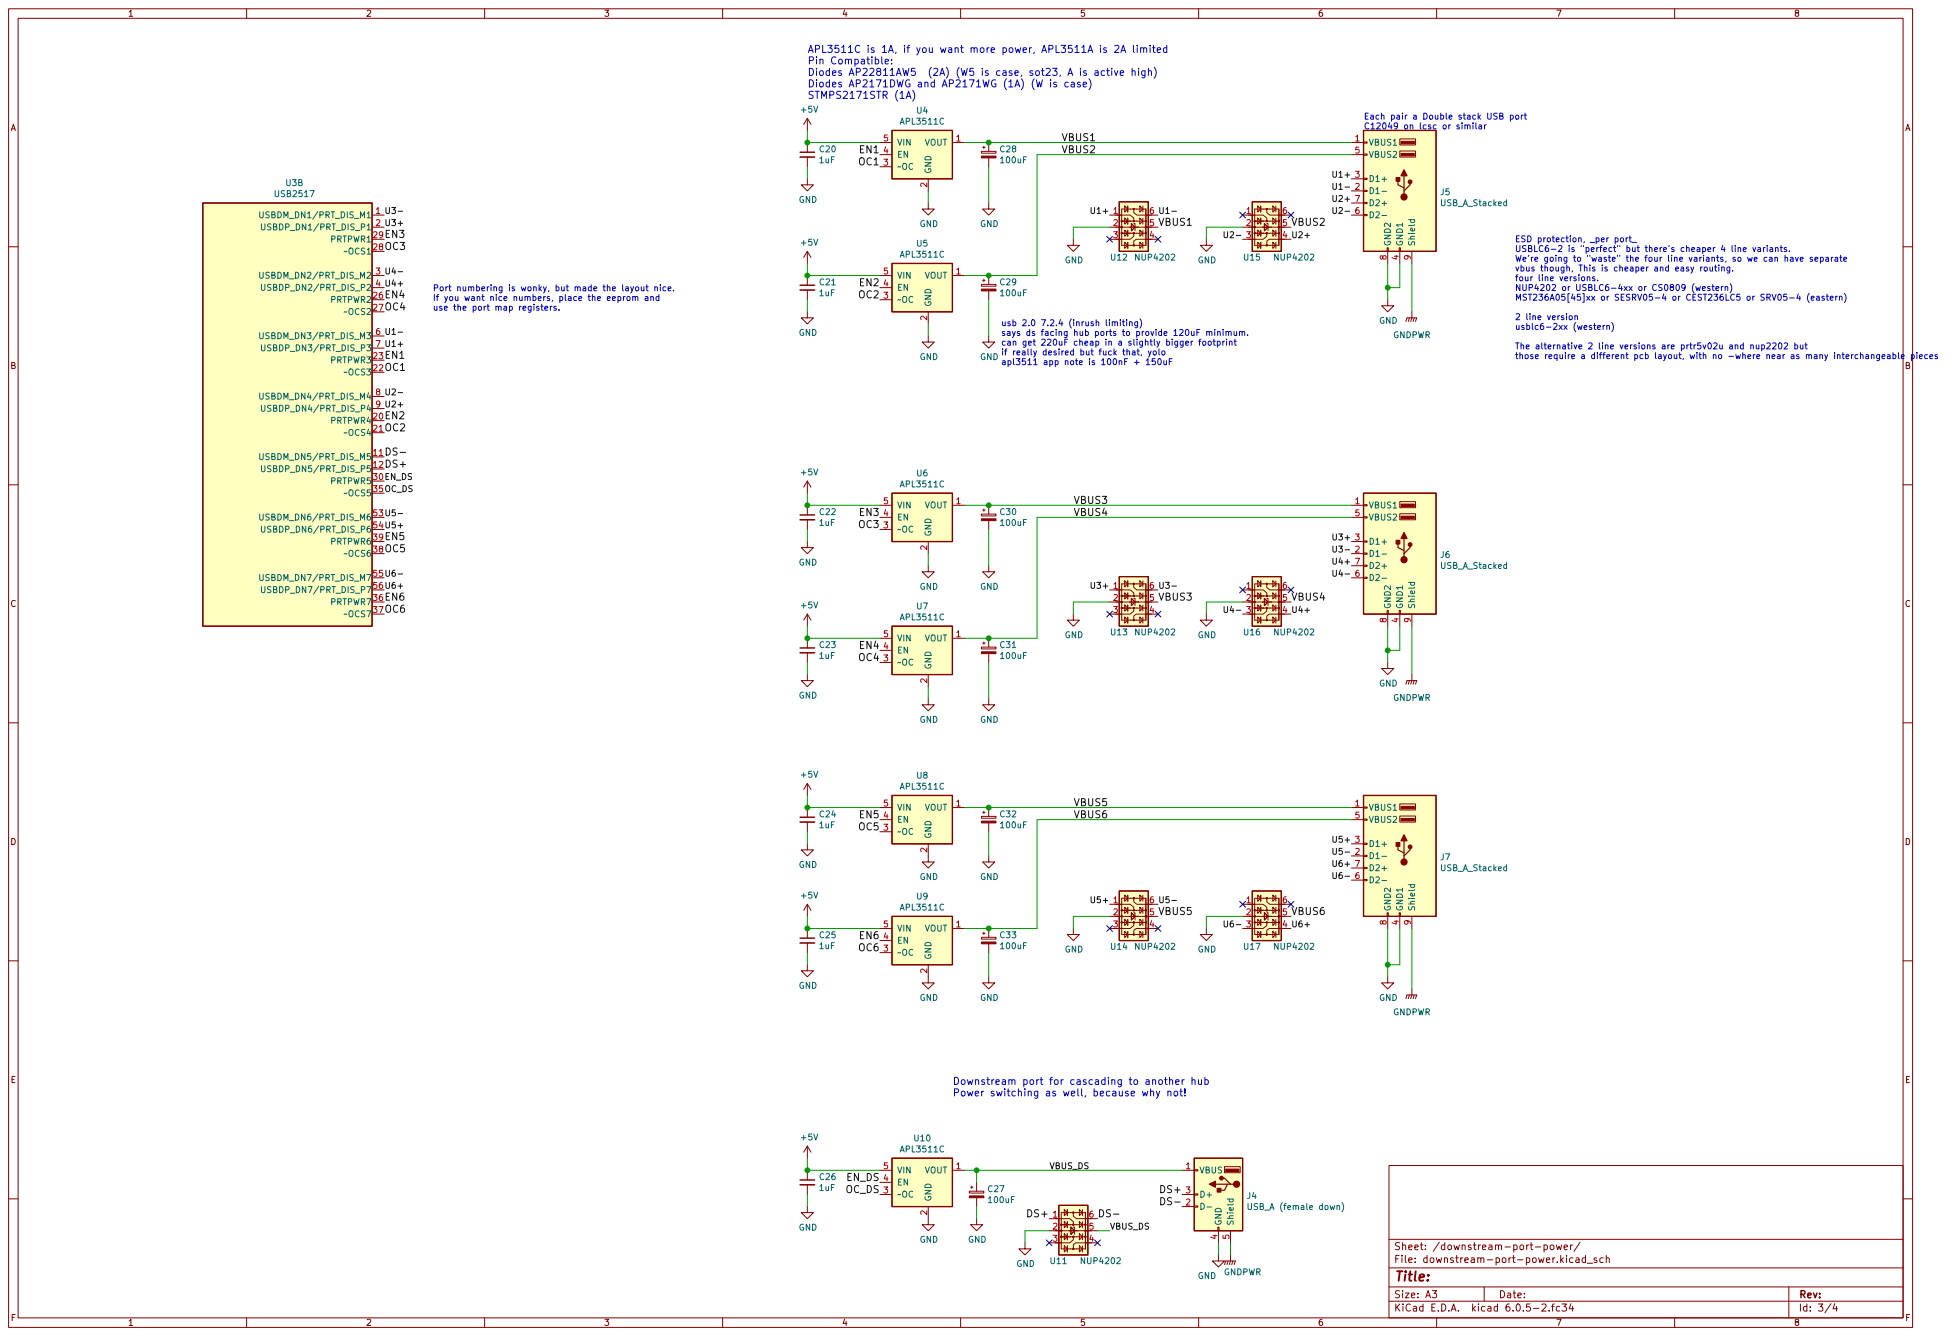
[picture p26: page 3]

APL3511C is 1A, if you want more power, APL3511A is 2A limited
Pin Compatible:
Diodes AP22811AW5 (2A) (W5 is case, sot23, A is active high)
Diodes AP2171DWG and AP2171WG (1A) (W is case)
STMPS2171STR (1A)
GND

Each pair a Double stack USB port C12049 on lcsc or similar Port numbering is wonky, but made the layout nice.

2 ~OC 3 EN 4 VIN 5 U4 APL3511C GND GND

ESD protection, _per port_
USBLC6-2 is "perfect" but there's cheaper 4 line variants.
We're going to "waste" the four line variants, so we can have separate
vbus though, This is cheaper and easy routing.
four line versions. NUP4202 or USBLC6-4xx or CS0809 (western)

If you want nice numbers, place the eeprom and
use the port map registers.

MST236A05[45]xx or SESRV05-4 or CEST236LC5 or SRV05-4 (eastern) 2 line version

says ds facing hub ports to provide 120uF minimum.
can get 220uF cheap in a slightly bigger footprint
if really desired but fuck that, yolo
apl3511 app note is 100nF + 150uF

The alternative 2 line versions are prtr5v02u and nup2202 but
those require a different pcb layout, with no -where near as many interchangeable pieces

2 ~OC 3 EN 4 VIN 5 U7 APL3511C GND

2 ~OC 3 EN 4 VIN 5 U9 APL3511C GND

2 ~OC 3 EN 4 VIN 5 U8 APL3511C GND

Sheet: /downstream-port-power/ GND

Downstream port for cascading to another hub
Power switching as well, because why not!

2 ~OC 3 EN 4 VIN 5 U10 APL3511C GND

File: downstream-port-power.kicad_sch
Id: 3/4 Title:

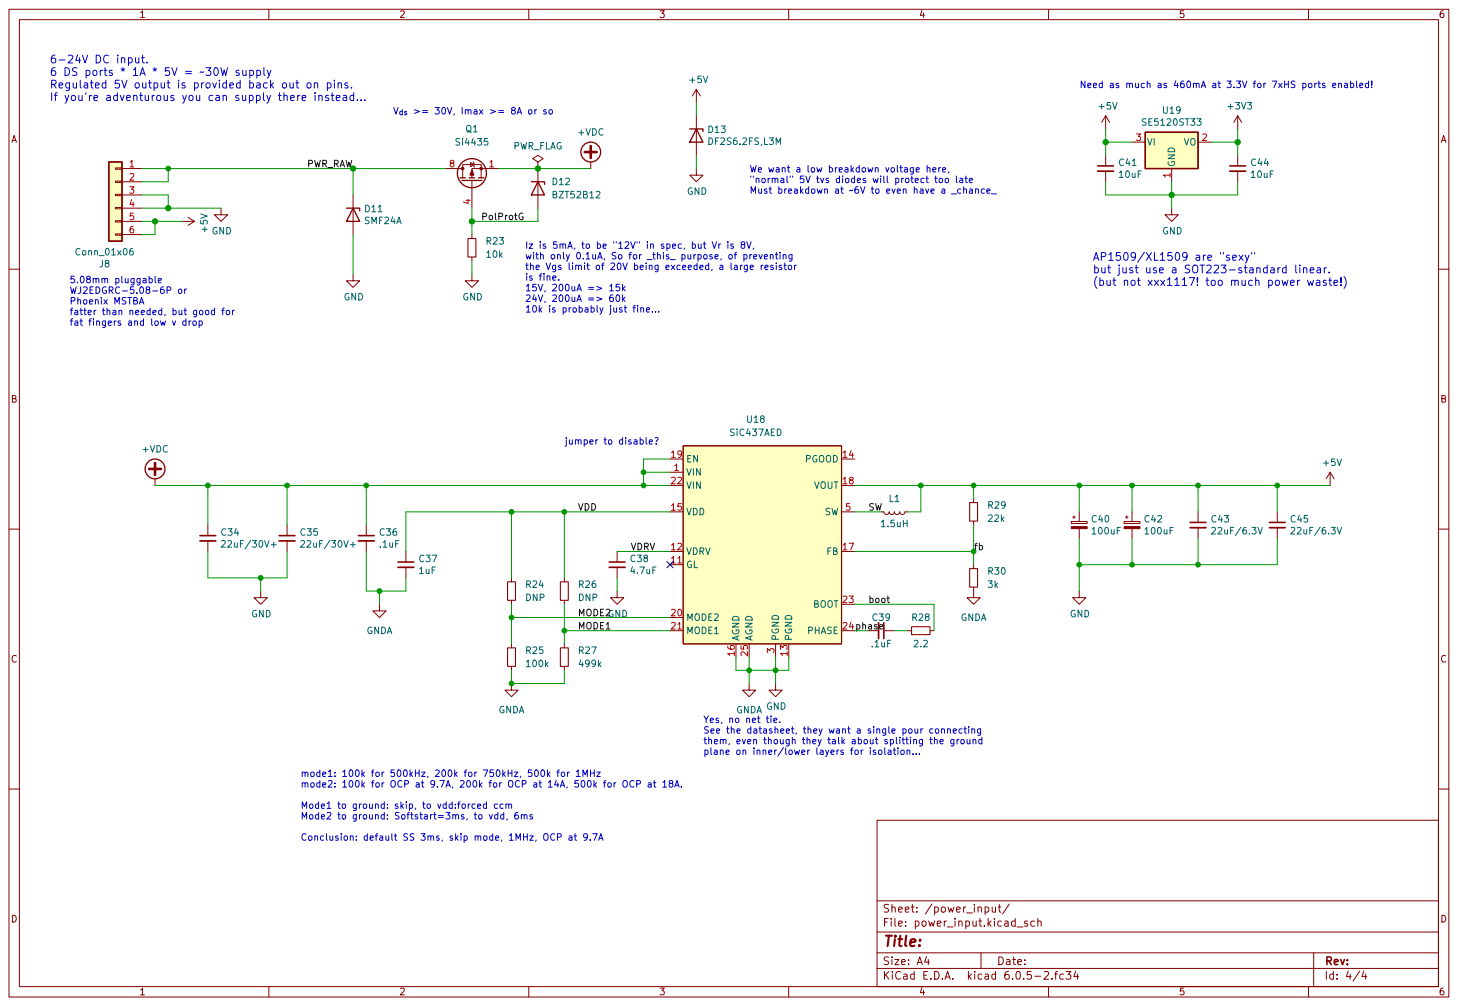
[picture p27: page 4]

"normal" 5V tvs diodes will protect too late Must breakdown at ~6V to even have a _chance_ 6-24V DC input.
6 DS ports * 1A * 5V = ~30W supply
Regulated 5V output is provided back out on pins.
If you're adventurous you can supply there instead...

Need as much as 460mA at 3.3V for 7xHS ports enabled!

We want a low breakdown voltage here,

Iz is 5mA, to be "12V" in spec, but Vr is 8V,
with only 0.1uA, So for _this_ purpose, of preventing
the Vgs limit of 20V being exceeded, a large resistor
is fine. 15V, 200uA => 15k 24V, 200uA => 60k 10k is probably just fine...

AP1509/XL1509 are "sexy"
but just use a SOT223-standard linear.
(but not xxx1117! too much power waste!)

5.08mm pluggable WJ2EDGRC-5.08-6P or Phoenix MSTBA

fatter than needed, but good for
fat fingers and low v drop

jumper to disable? mode1: 100k for 500kHz, 200k for 750kHz, 500k for 1MHz mode2: 100k for OCP at 9.7A, 200k for OCP at 14A, 500k for OCP at 18A. Mode1 to ground: skip, to vdd:forced ccm

them, even though they talk about splitting the ground
plane on inner/lower layers for isolation...

Mode2 to ground: Softstart=3ms, to vdd, 6ms

Conclusion: default SS 3ms, skip mode, 1MHz, OCP at 9.7A
