karlp/hubbish/parts/usb-a-female-2103011234_Jing-Extension-of-the-Electronic-Co--902-141A1011D10100_C42643.pdf

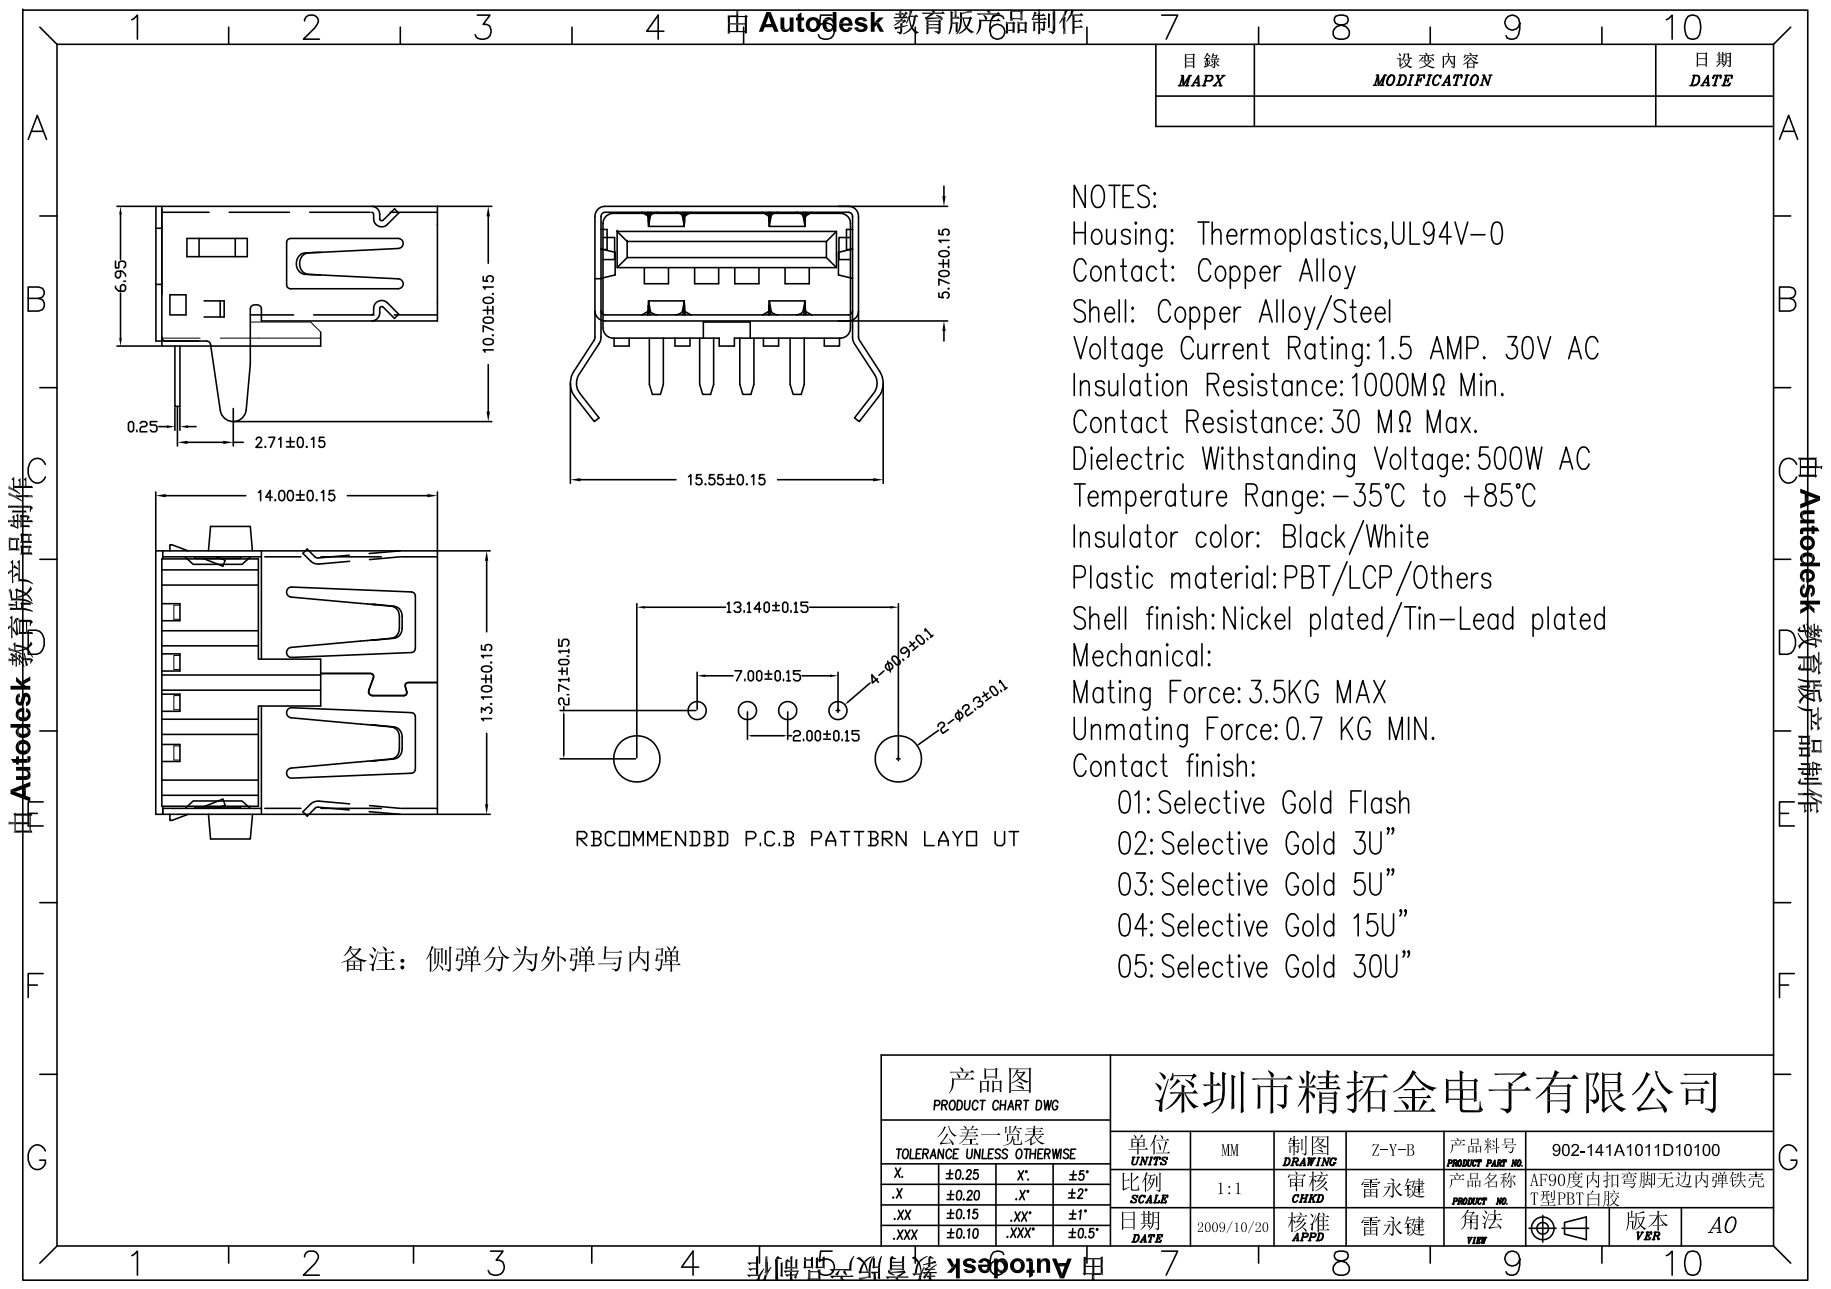
[picture p28: page 1]
