karlp/hubbish/parts/usb-double-a-2102261732_Jing-Extension-of-the-Electronic-Co--907-111A1022D10200_C12049.pdf

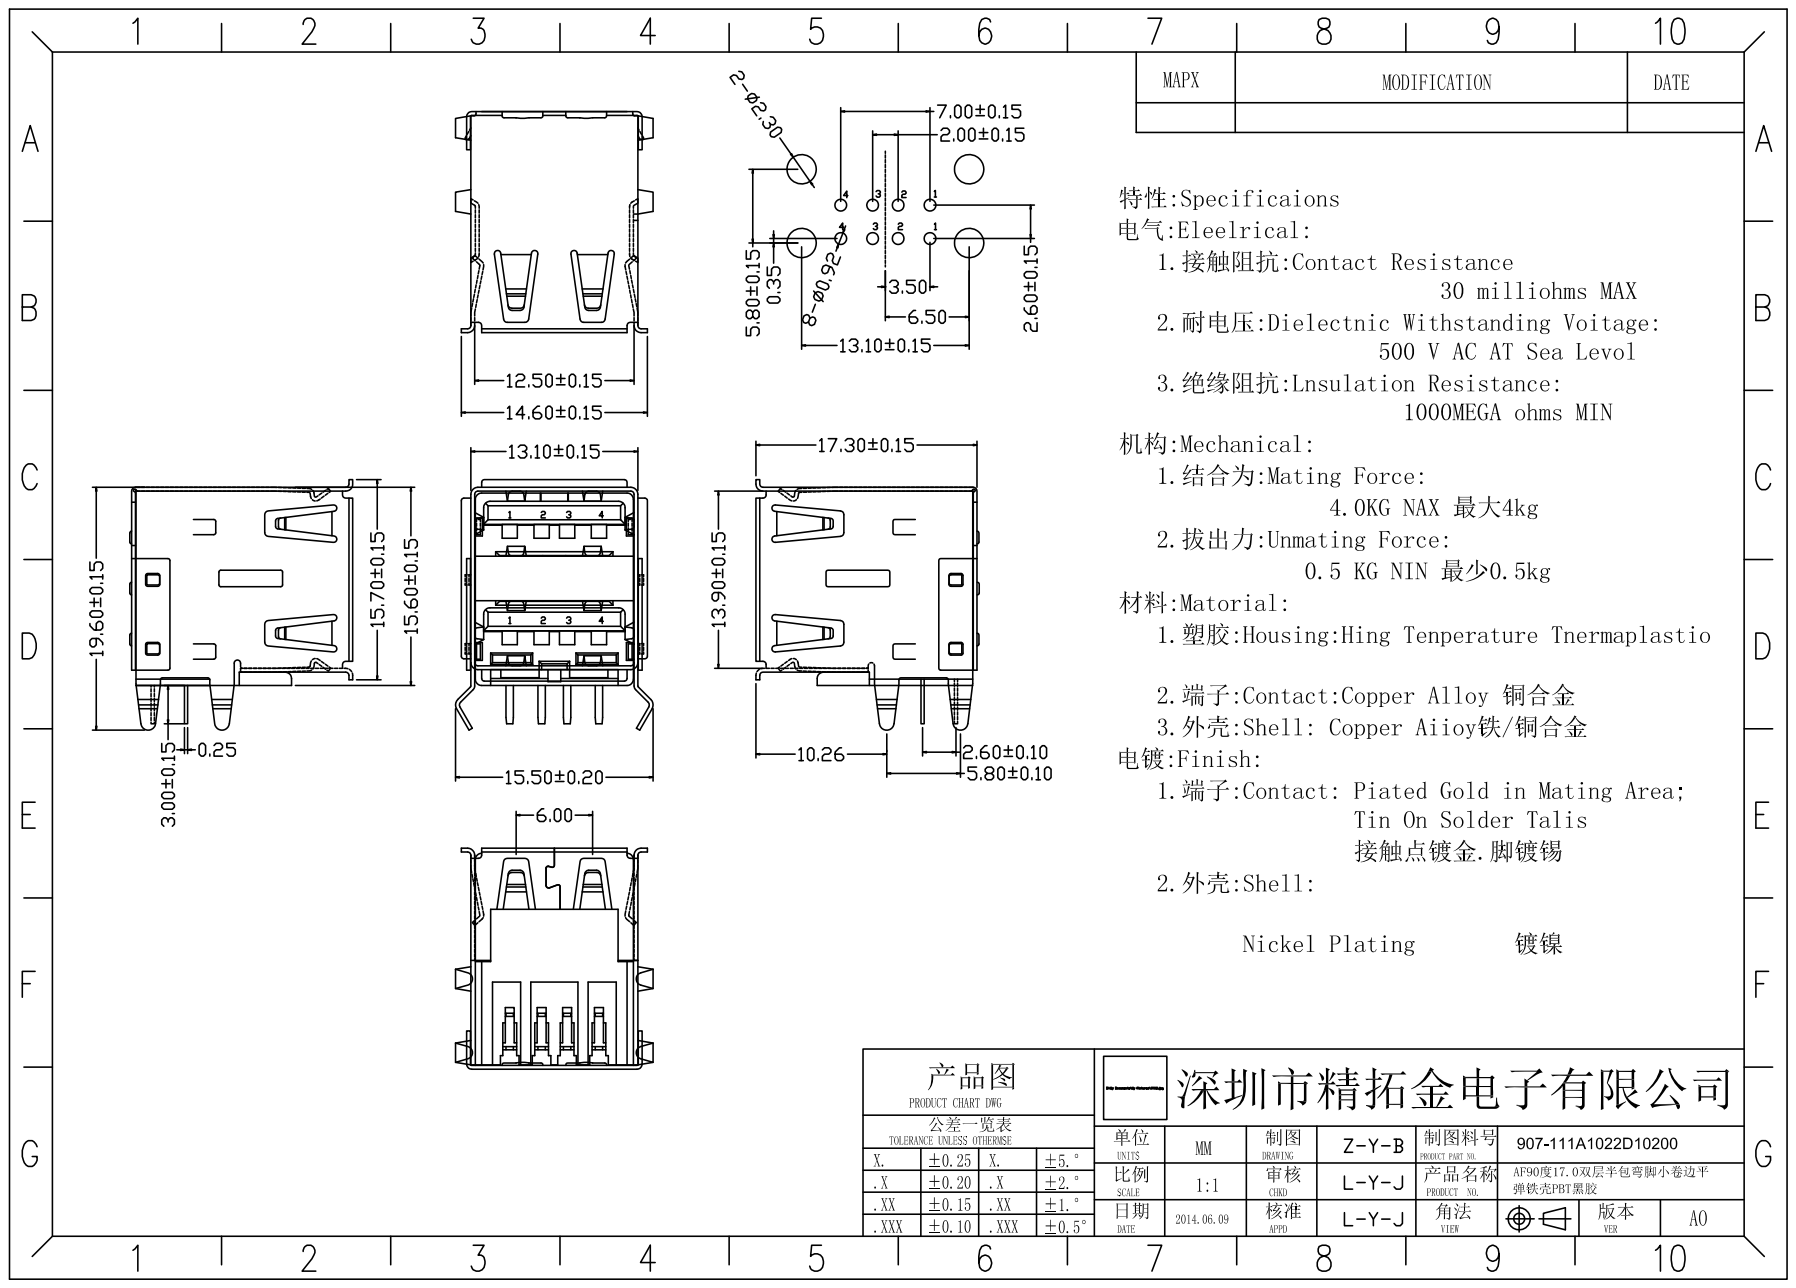
[picture p29: page 1]
