karlp/hubbish/parts/enclosures/bud-hb388.pdf

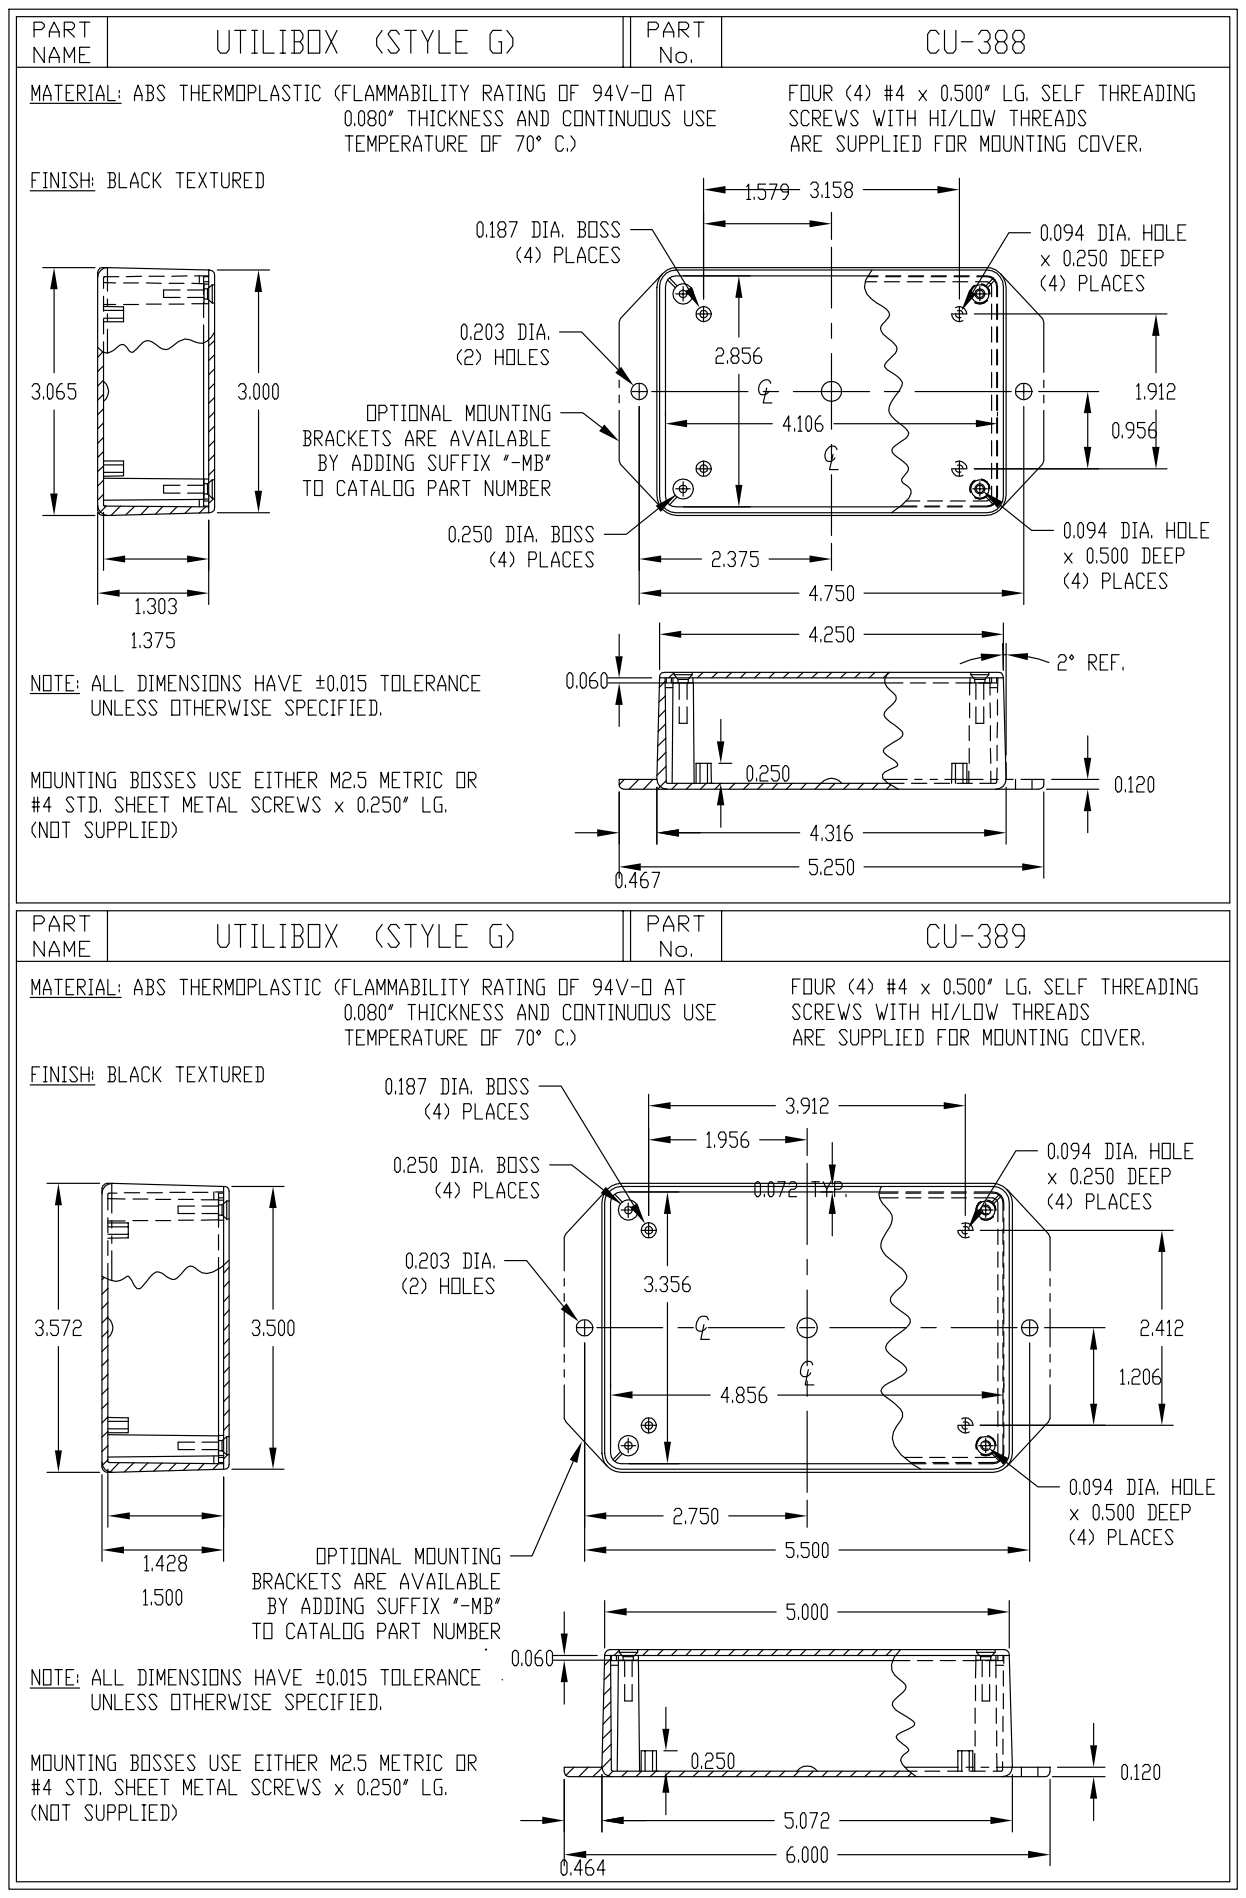
[picture p30: page 1]
